the78mole/km271-wifi/DOC/KM271 Oil Burner has error.PNG

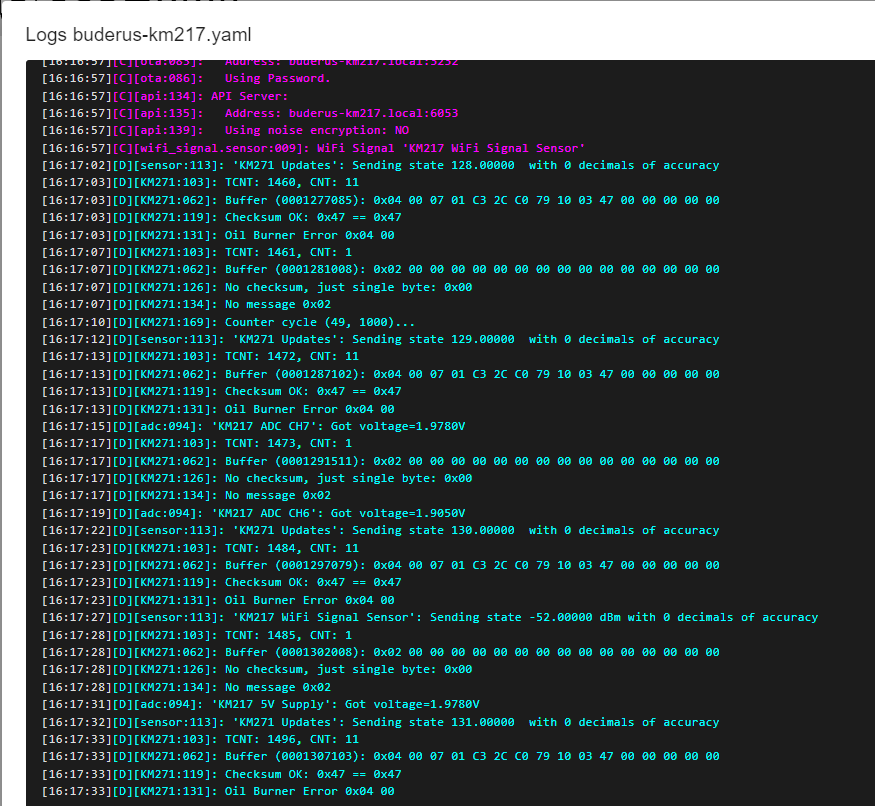
DOC/KM271 Oil Burner has error.PNG
