the78mole/km271-wifi/EXTENSIONS/ETH_W5500/Export/ETH_W5500.png

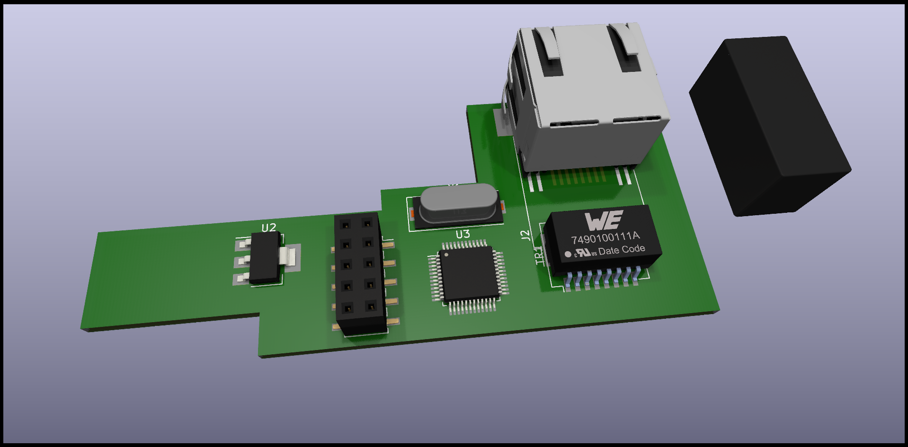
EXTENSIONS/ETH_W5500/Export/ETH_W5500.png
