the78mole/km271-wifi/EXTENSIONS/ETH_W5500/IMG/ETH_Extension_Rendering.PNG

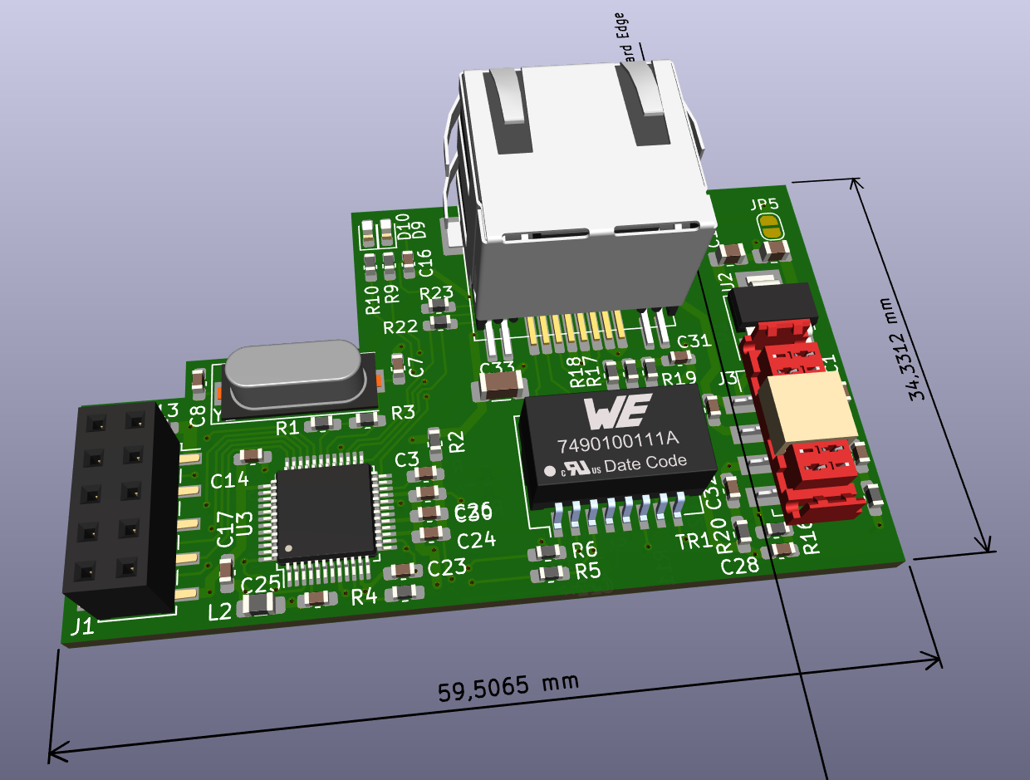
EXTENSIONS/ETH_W5500/IMG/ETH_Extension_Rendering.PNG
