the78mole/km271-wifi/IMG/FM244/FM244 Front.jpg

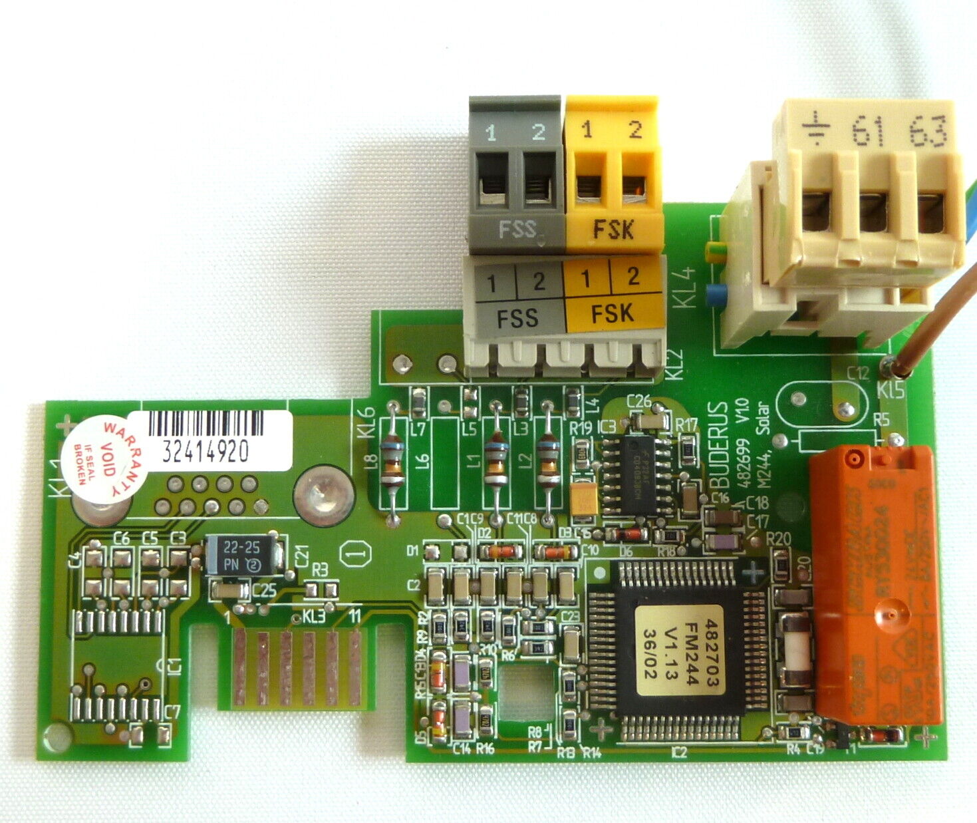
IMG/FM244/FM244 Front.jpg
