the78mole/km271-wifi/IMG/IMG_20220502_030331.jpg

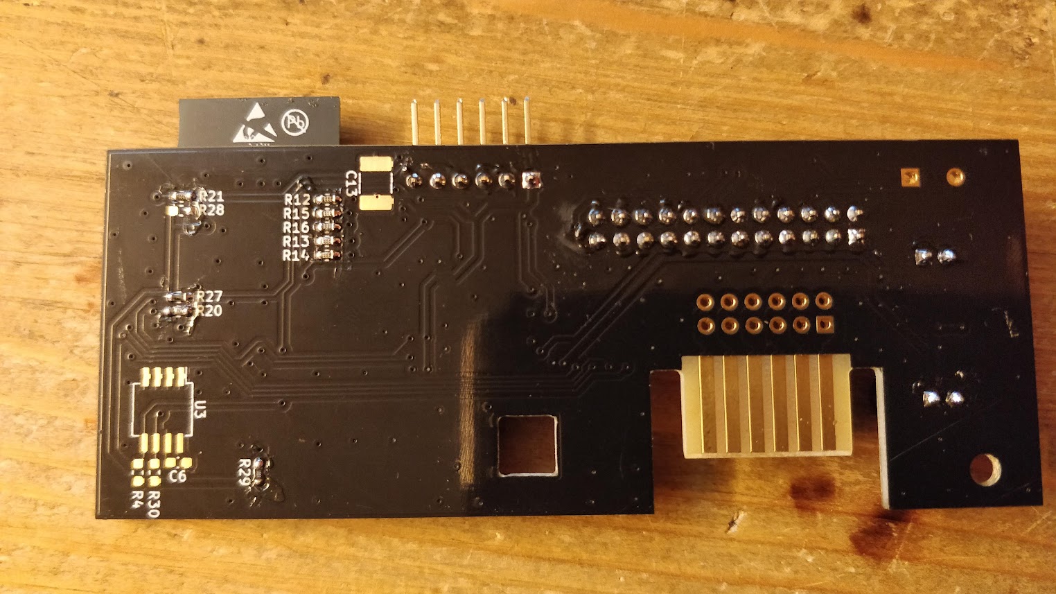
IMG/IMG_20220502_030331.jpg
