the78mole/km271-wifi/IMG/KM271-WiFi-0.0.6.jpg

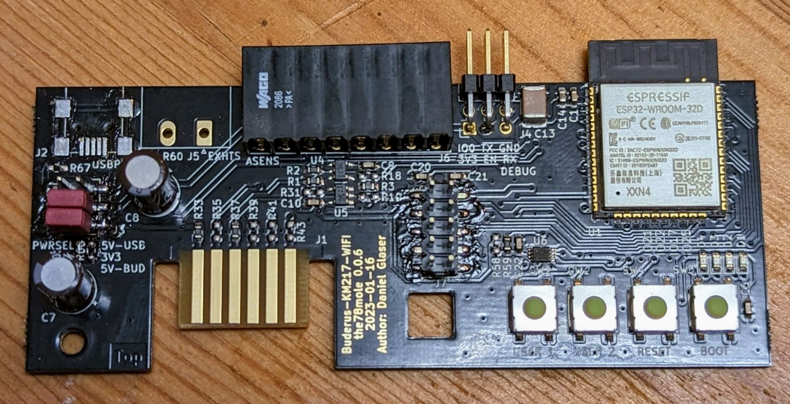
IMG/KM271-WiFi-0.0.6.jpg
