the78mole/km271-wifi/IMG/KM271-WiFi-0.0.7 Back.jpg

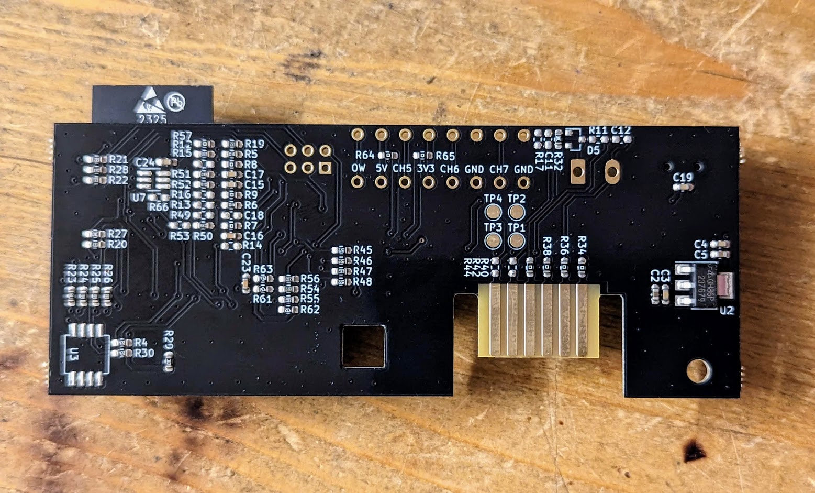
IMG/KM271-WiFi-0.0.7 Back.jpg
