the78mole/km271-wifi/IMG/KM271-WiFi-0.0.7_3D.png

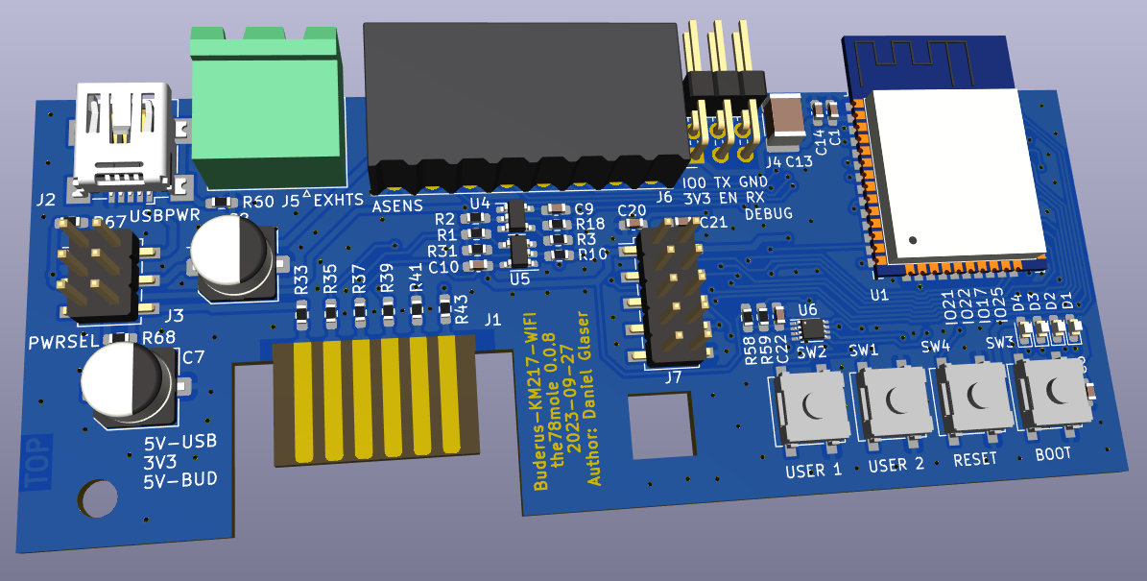
IMG/KM271-WiFi-0.0.7_3D.png
