the78mole/km271-wifi/IMG/KM271-WiFi-0.1.0-back.jpg

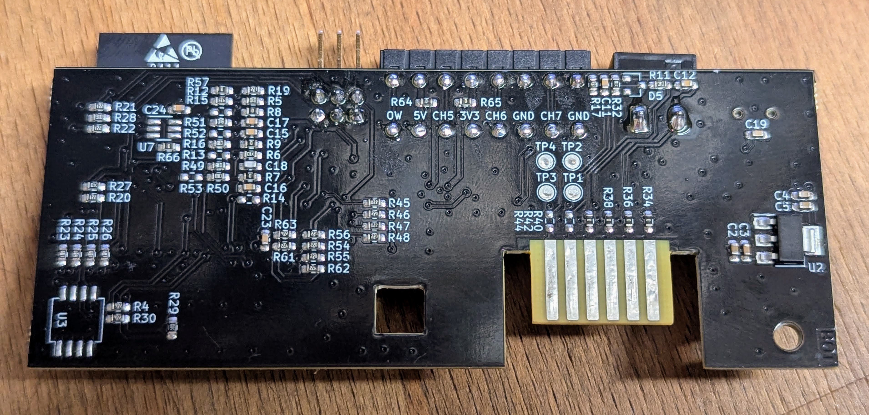
IMG/KM271-WiFi-0.1.0-back.jpg
