the78mole/km271-wifi/IMG/KM271-WiFi_0.0.5_top.jpg

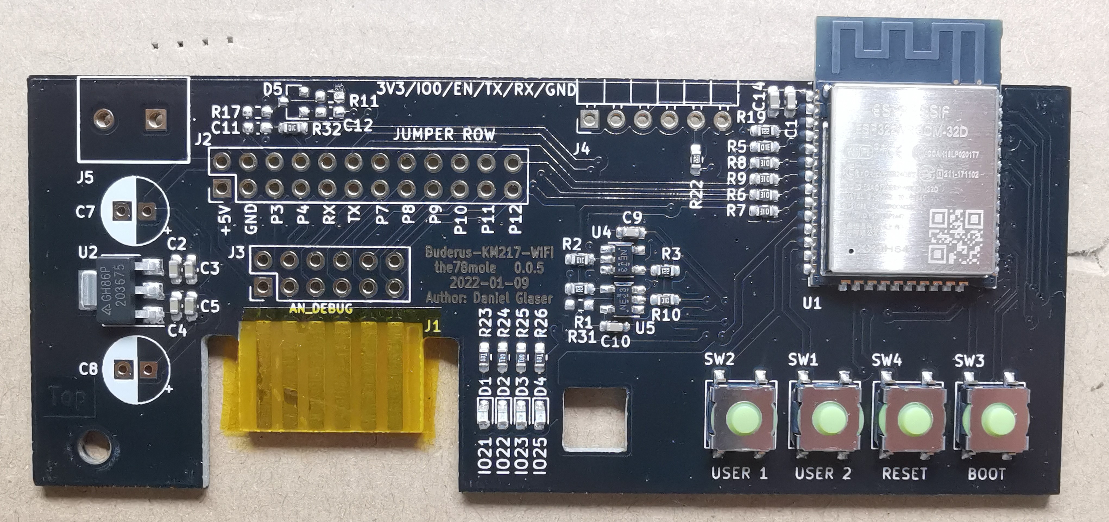
IMG/KM271-WiFi_0.0.5_top.jpg
