the78mole/km271-wifi/IMG/M292/M292_bottom_crop.jpg

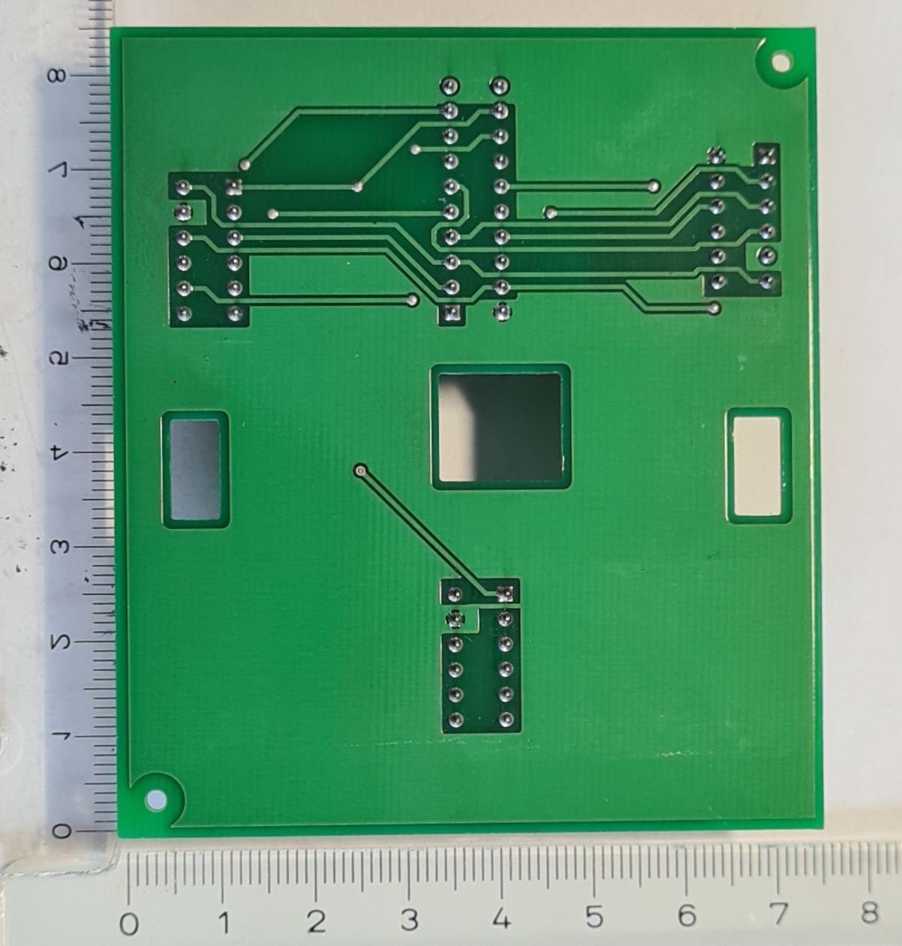
IMG/M292/M292_bottom_crop.jpg
