the78mole/km271-wifi/IMG/M292/M292_top_2_crop.jpg

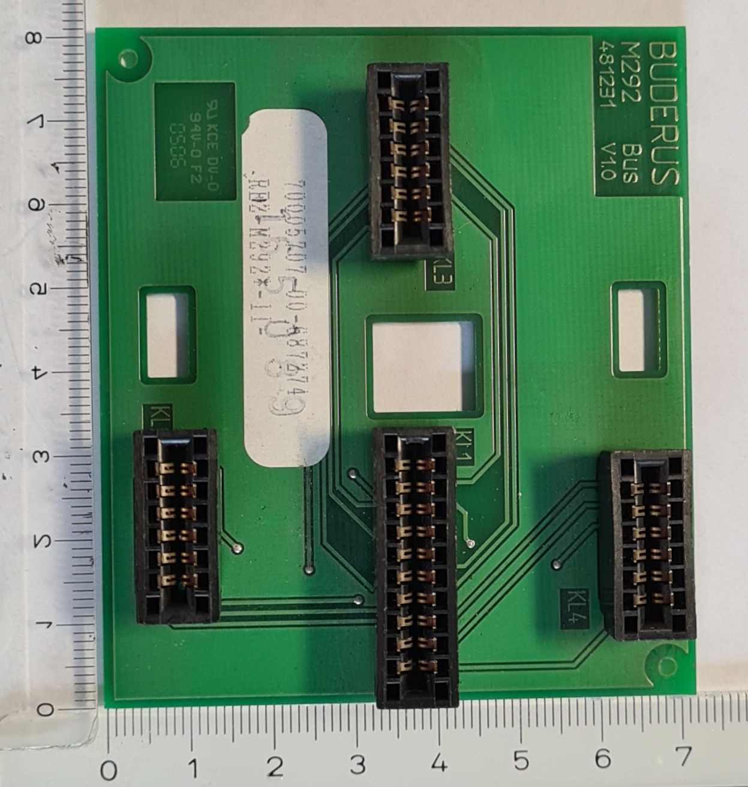
IMG/M292/M292_top_2_crop.jpg
