the78mole/km271-wifi/IMG/PCB_0.0.6.jpg

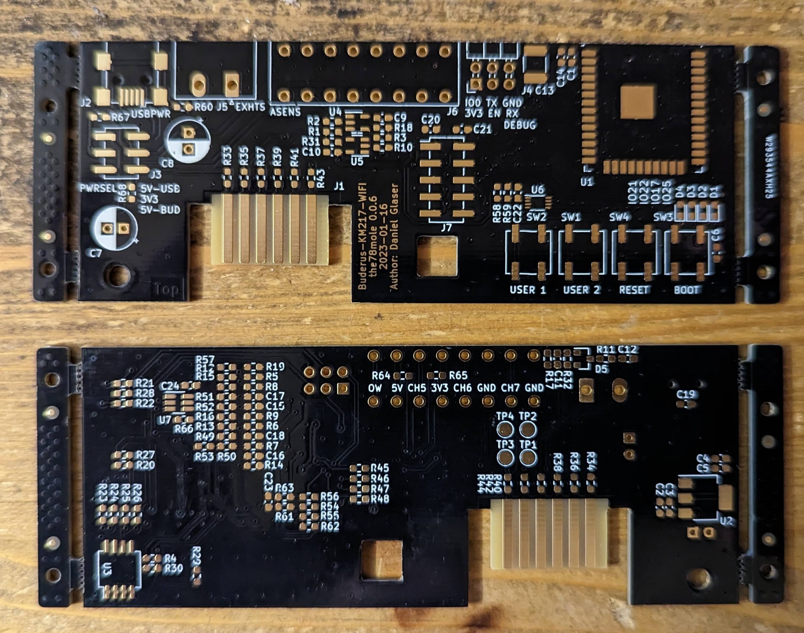
IMG/PCB_0.0.6.jpg
