the78mole/km271-wifi/EXTENSIONS/ETH_W5500/DOC/w5500_sch_v110_use_trans_.pdf

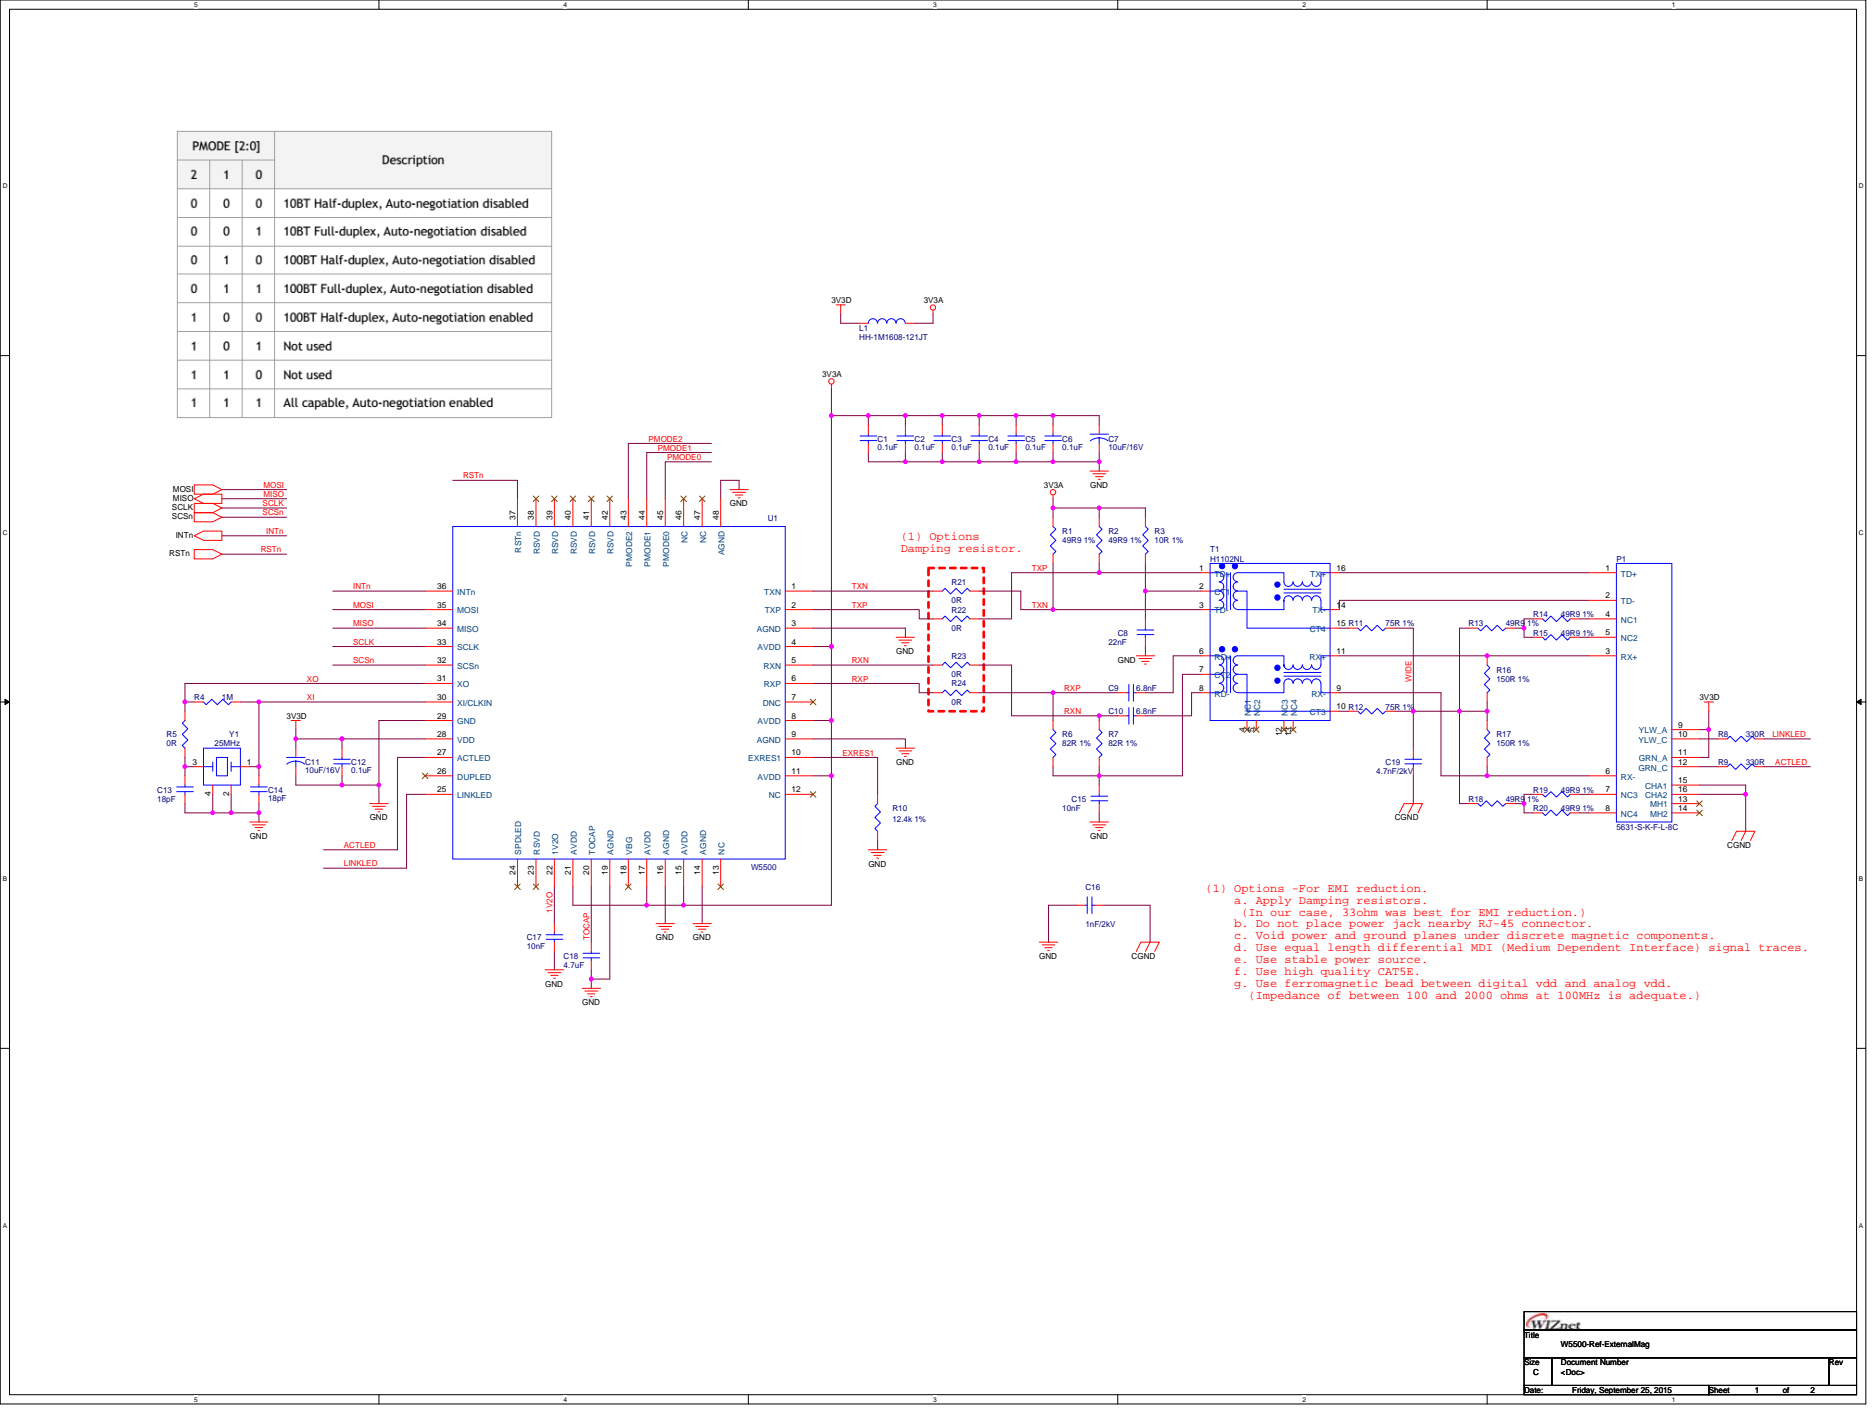
[picture p62: page 1]

(1) Options -For EMI reduction.
a. Apply Damping resistors.
(In our case, 33ohm was best for EMI reduction.)
b. Do not place power jack nearby RJ-45 connector.
c. Void power and ground planes under discrete magnetic components.
d. Use equal length differential MDI (Medium Dependent Interface) signal traces.
e. Use stable power source.
f. Use high quality CAT5E.
g. Use ferromagnetic bead between digital vdd and analog vdd.
(Impedance of between 100 and 2000 ohms at 100MHz is adequate.)
