the78mole/km271-wifi/EXTENSIONS/ETH_W5500/Export/ETH_W5500.pdf

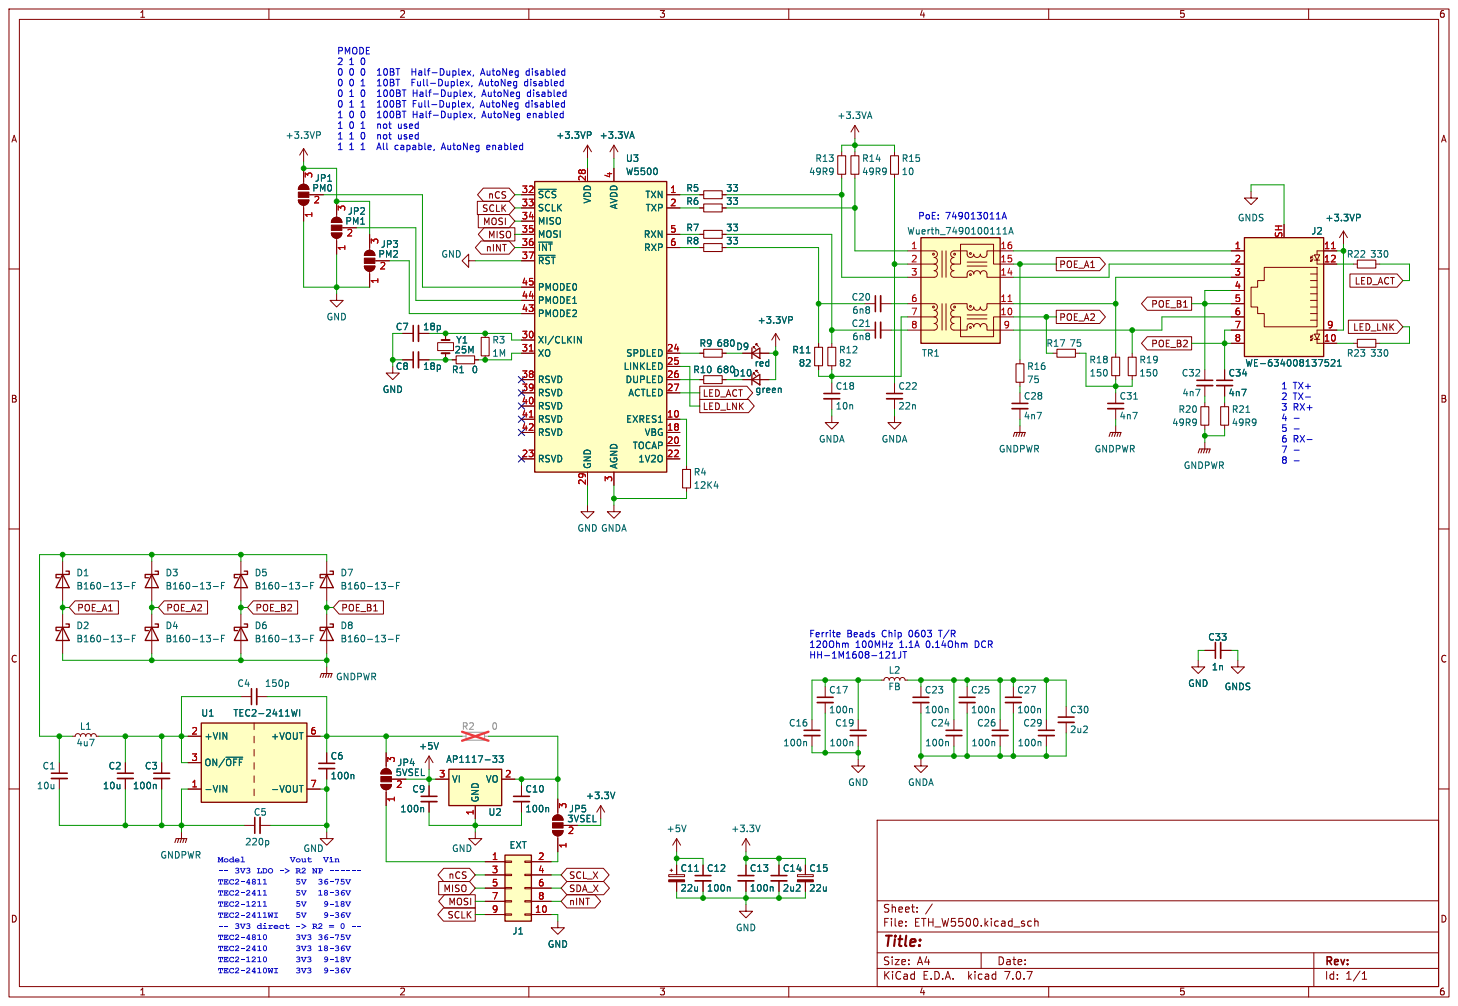
[picture p63: page 1]

4 RSVD 40 RSVD 41 RSVD 42 PMODE2 43 PMODE1 44 PMODE0 45 RXN 5 RXP 6 U3 W5500 R22 330 C34

4 RSVD 40 RSVD 41 RSVD 42 PMODE2 43 PMODE1 44 PMODE0 45 RXN 5 RXP 6 D10 GND green

3 XI/CLKIN 30 XO 31 ~{SCS} 32 SCLK 33 MISO 34 MOSI 35 ~{INT} 36 ~{RST} 37 RSVD 38 RSVD 39 AVDD

4 - 5 - 6 RX- 7 - 8 - Ferrite Beads Chip 0603 T/R
