the78mole/km271-wifi/KM217-WiFi/Export/KM217-WiFi - PCB 0.0.7.pdf

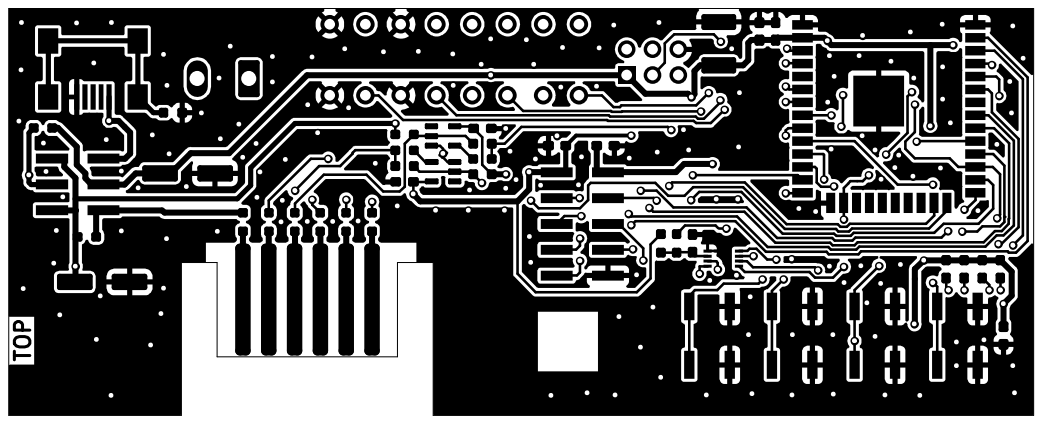
[picture p66: page 1]

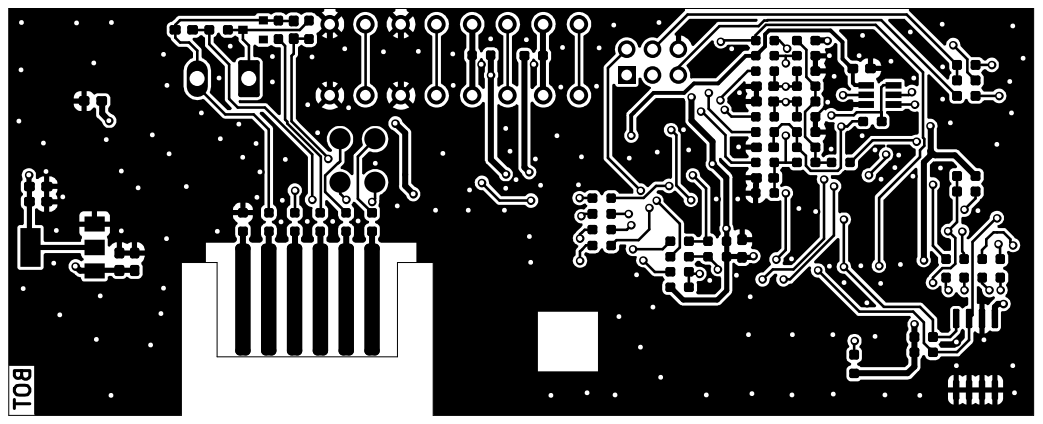
[picture p67: page 2]

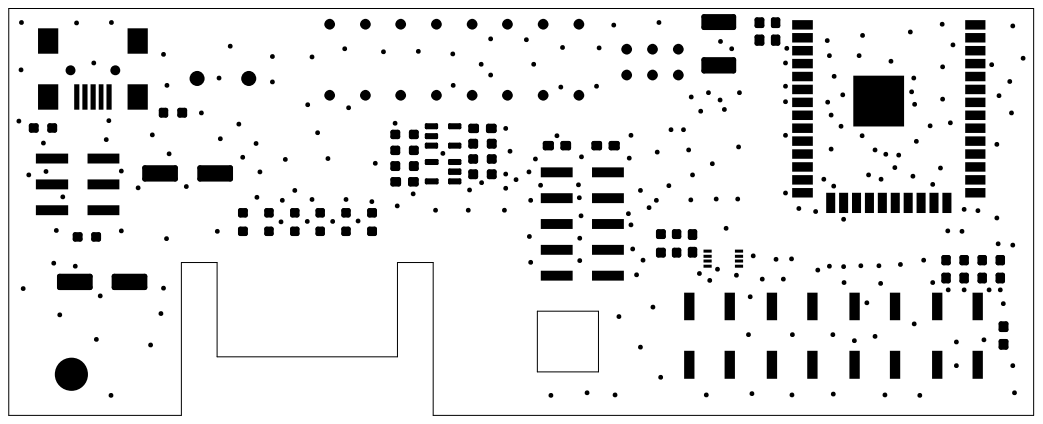
[picture p68: page 3]

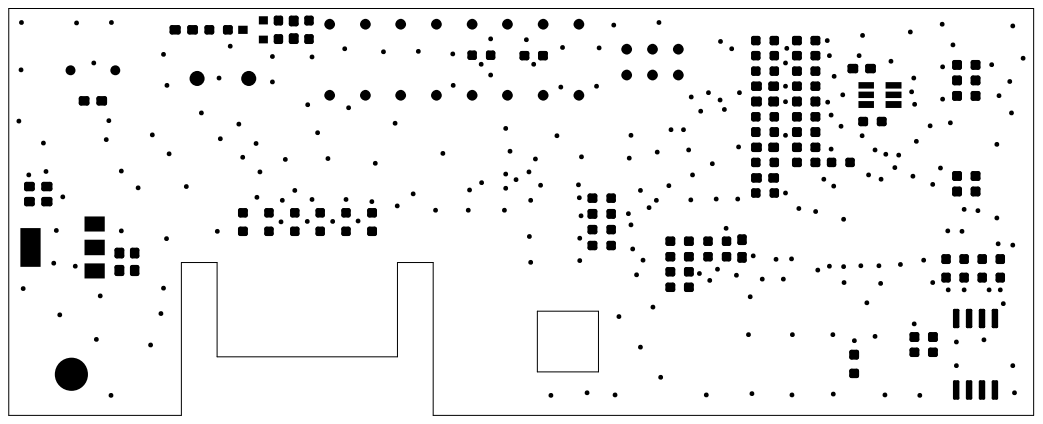
[picture p69: page 4]

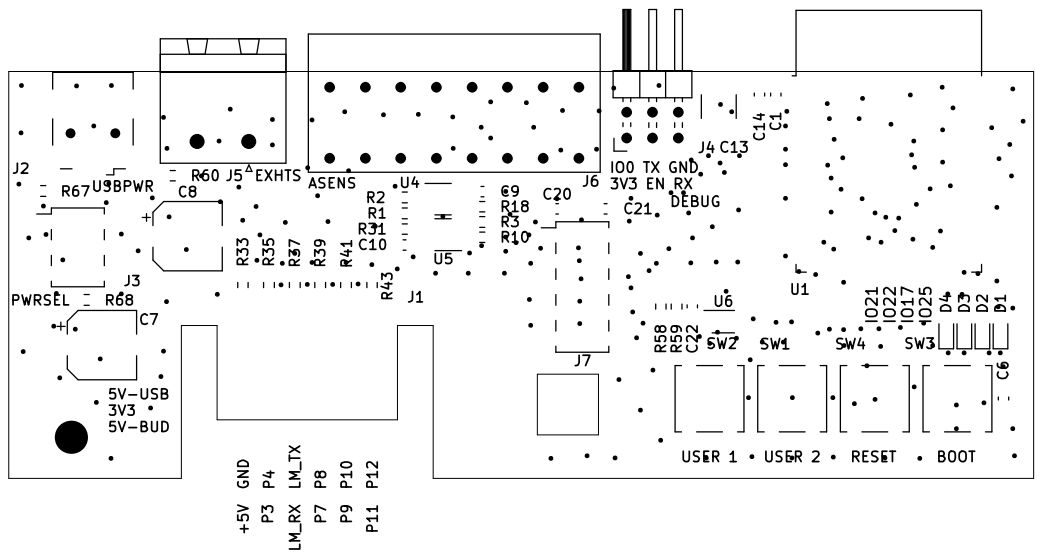
[picture p70: page 5]

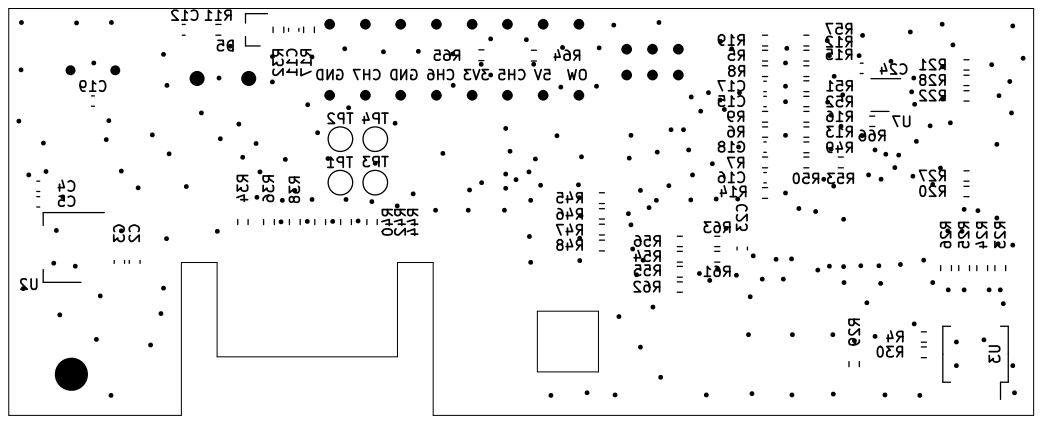
[picture p71: page 6]

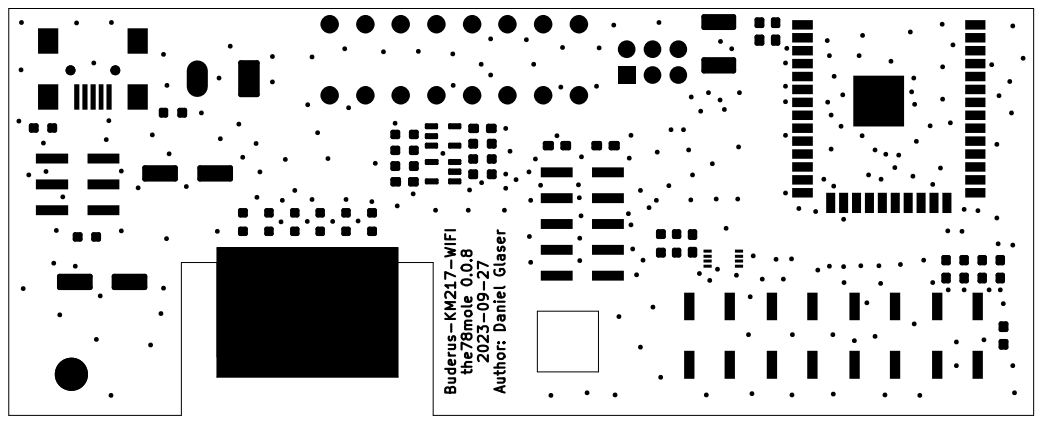
[picture p72: page 7]

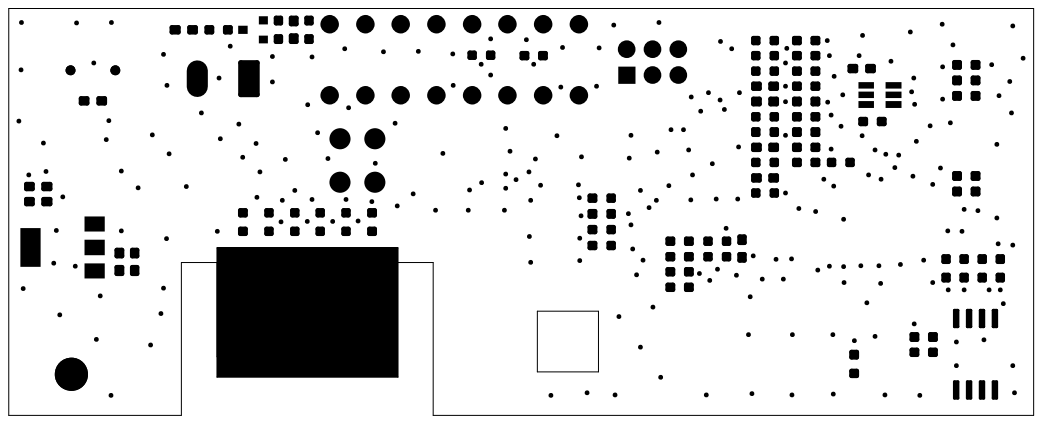
[picture p73: page 8]

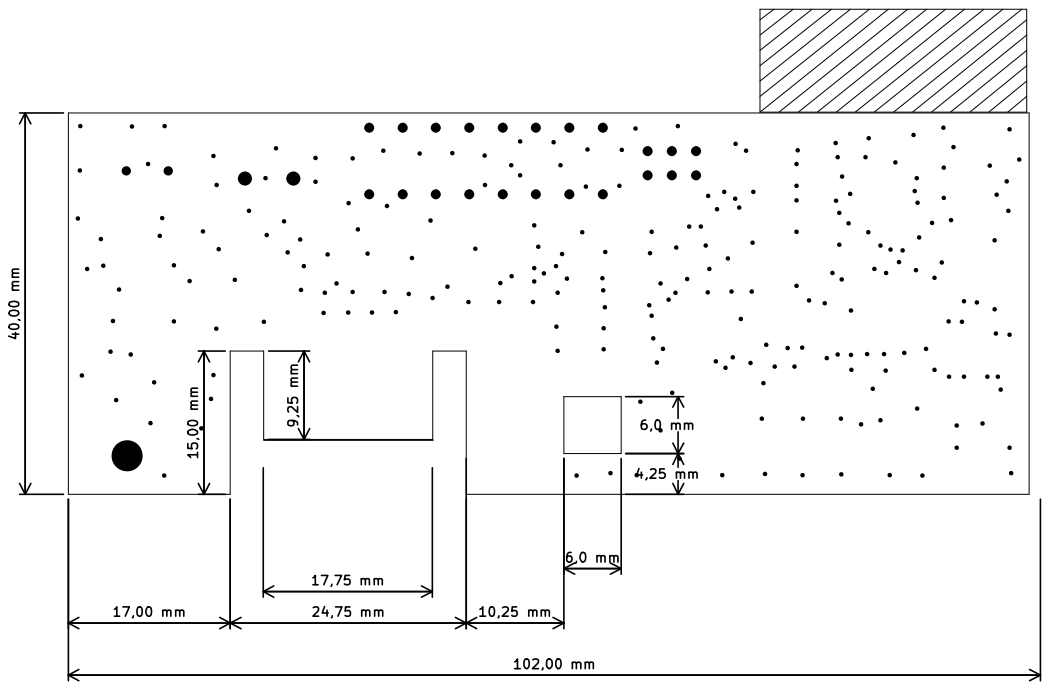
[picture p74: page 9]

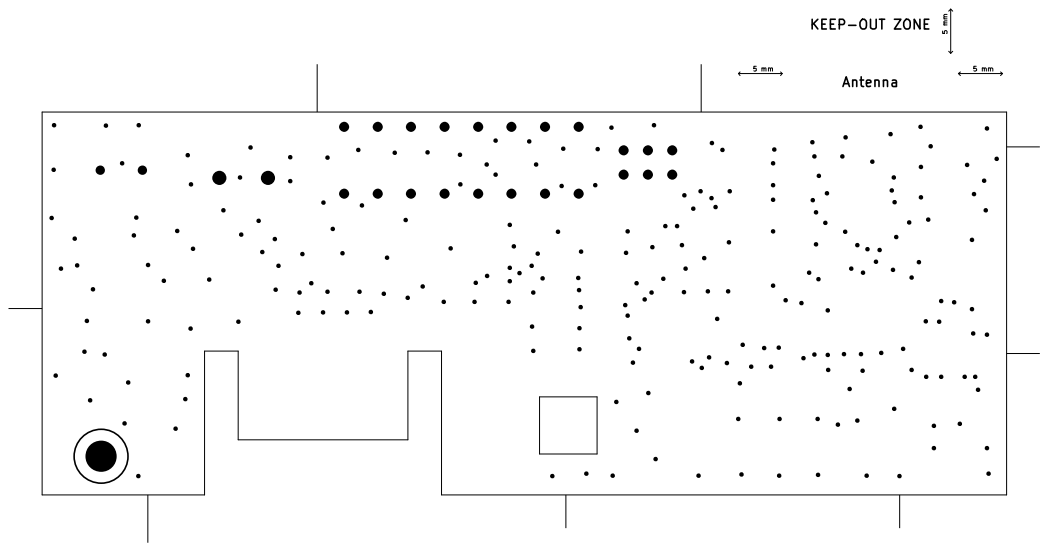
[picture p75: page 10]

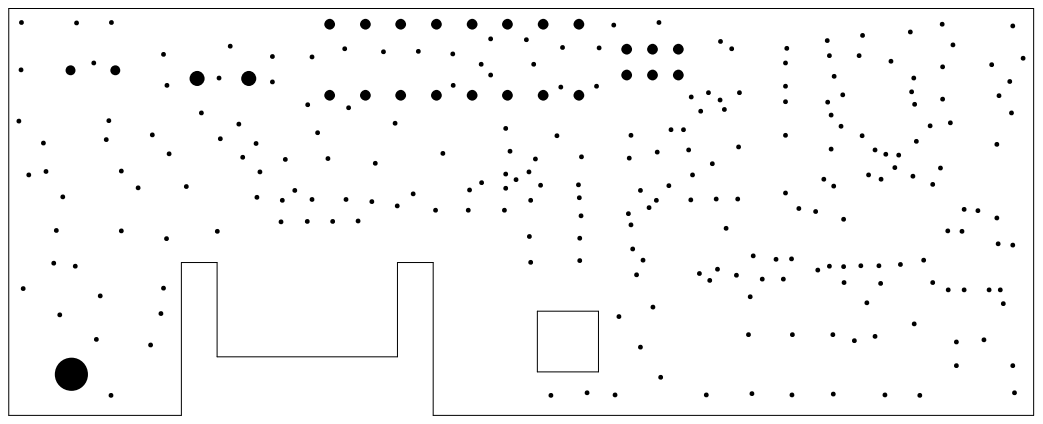
[picture p76: page 11]

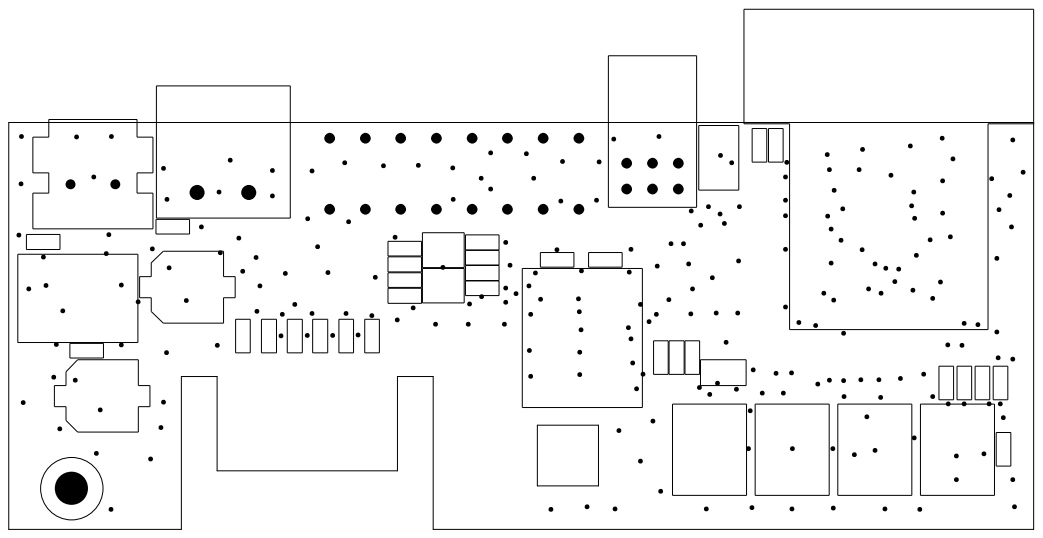
[picture p77: page 13]

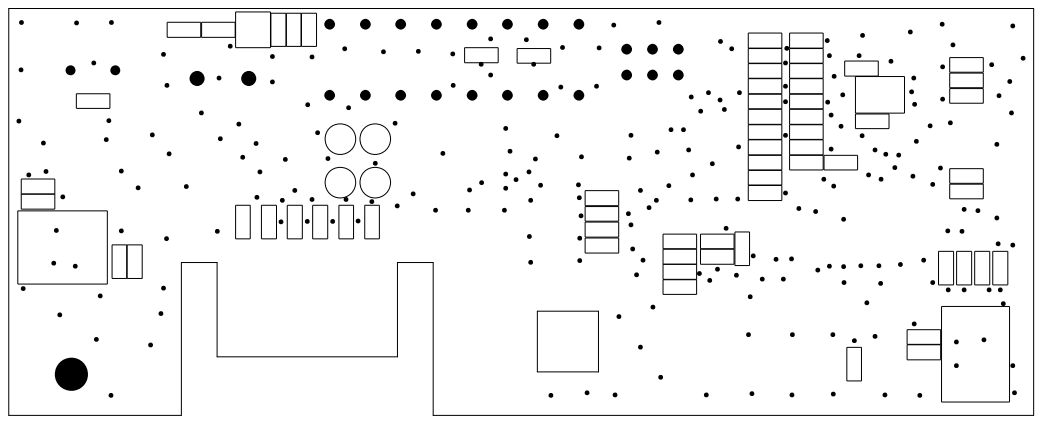
[picture p78: page 14]

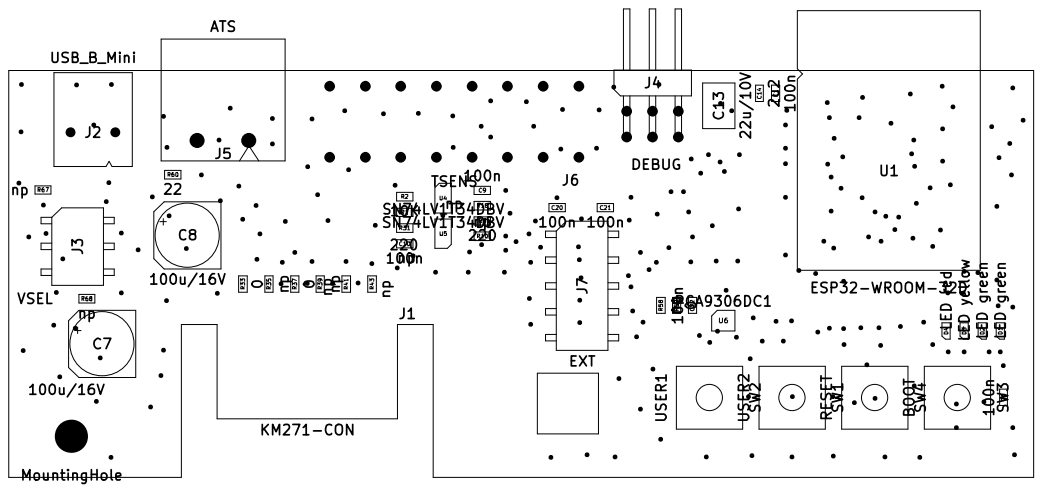
[picture p79: page 15]

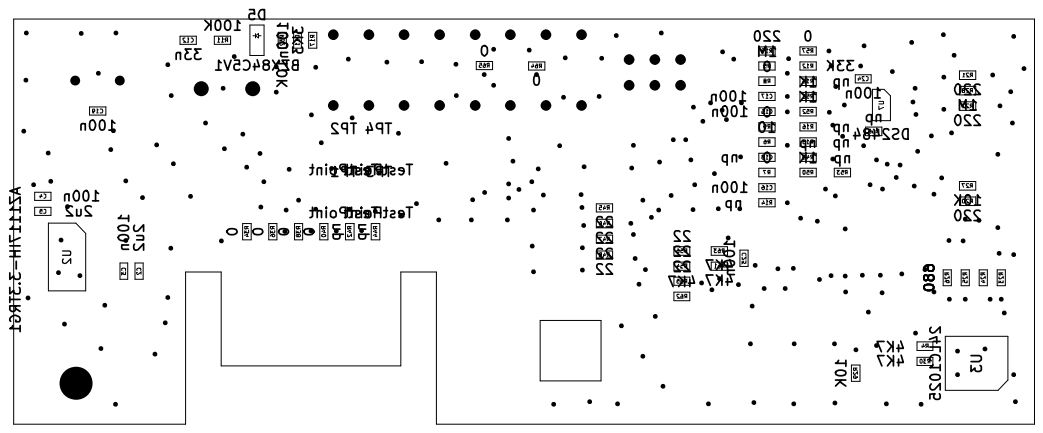
[picture p80: page 16]
