the78mole/km271-wifi/KM217-WiFi/Export/KM217-WiFi - PCB 0.0.5.pdf

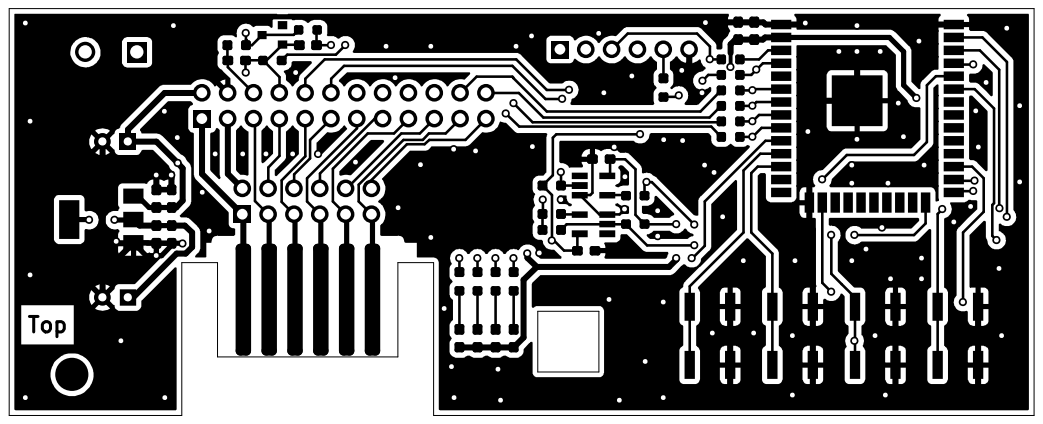
[picture p81: page 1]

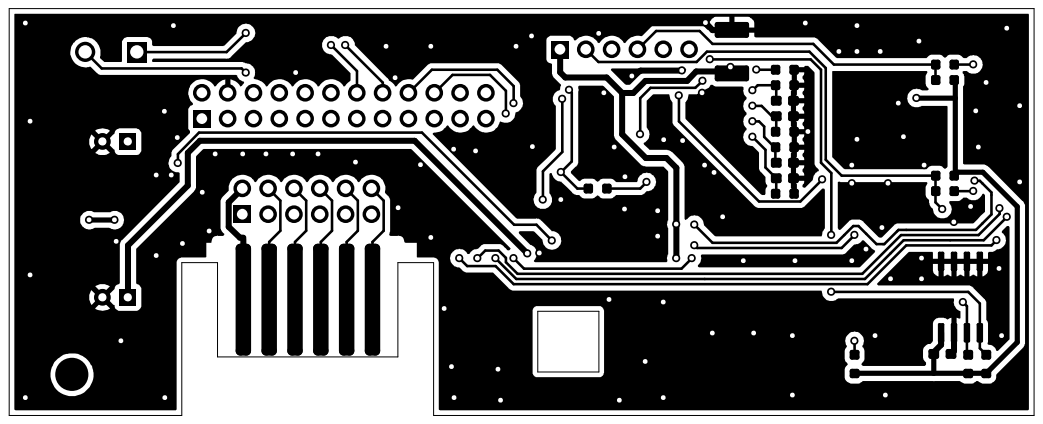
[picture p82: page 2]

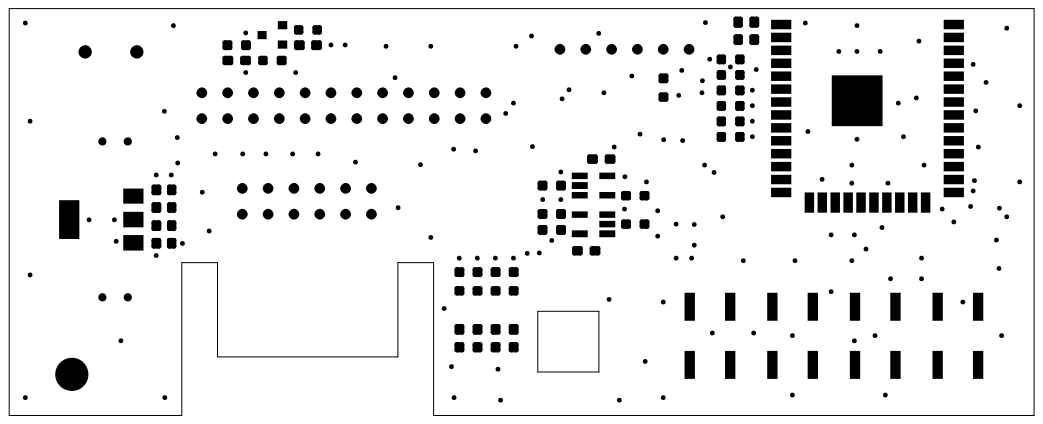
[picture p83: page 3]

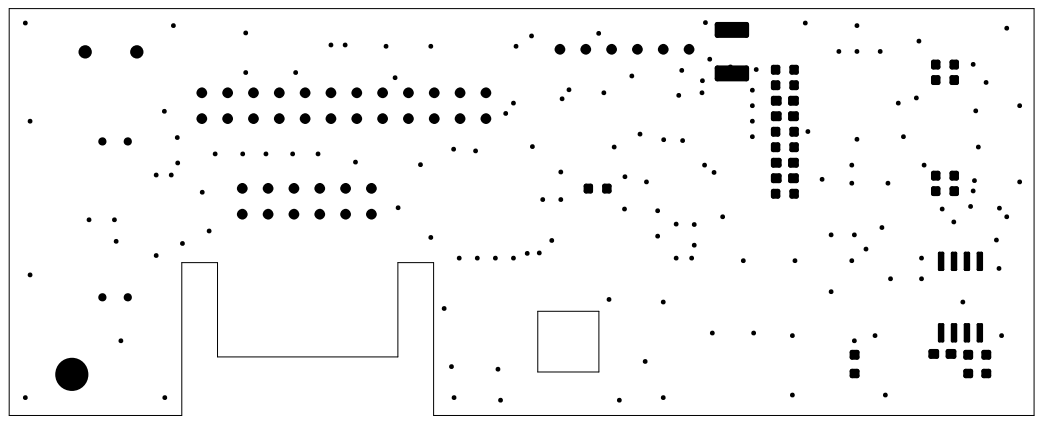
[picture p84: page 4]

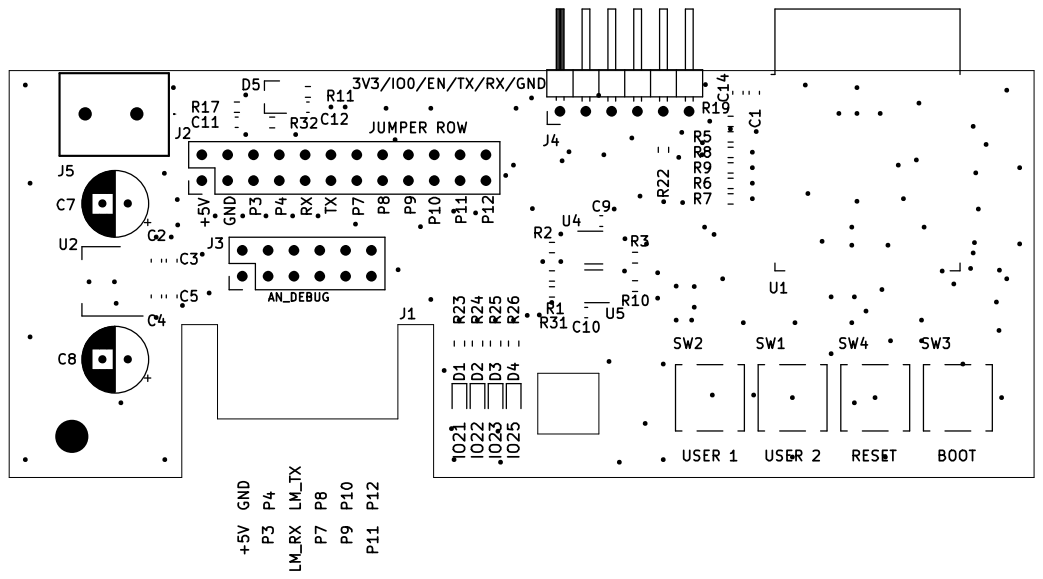
[picture p85: page 5]

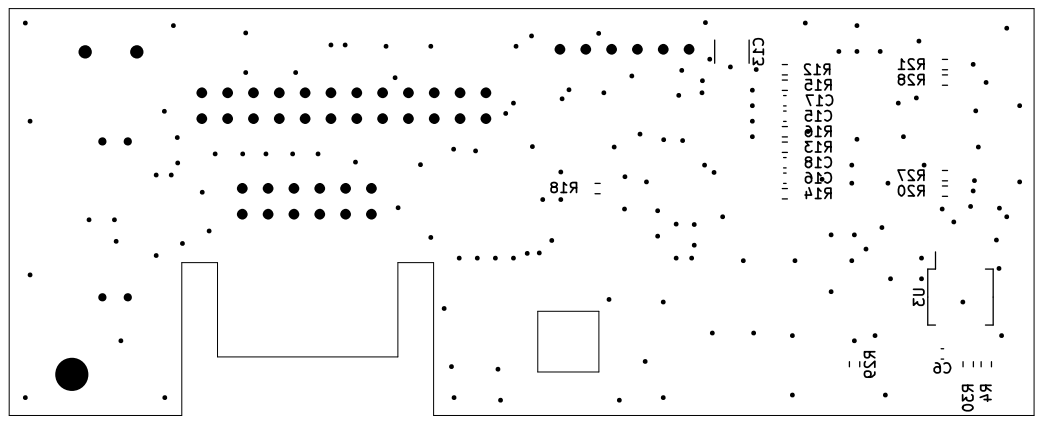
[picture p86: page 6]

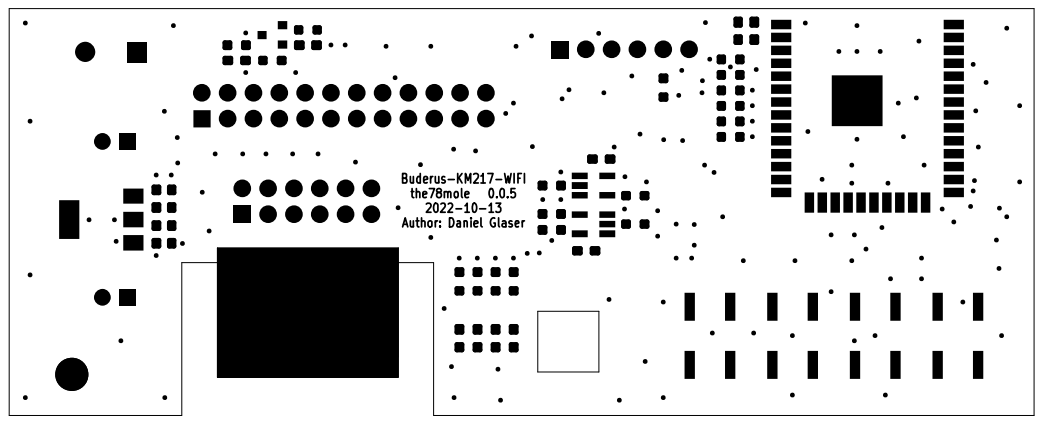
[picture p87: page 7]

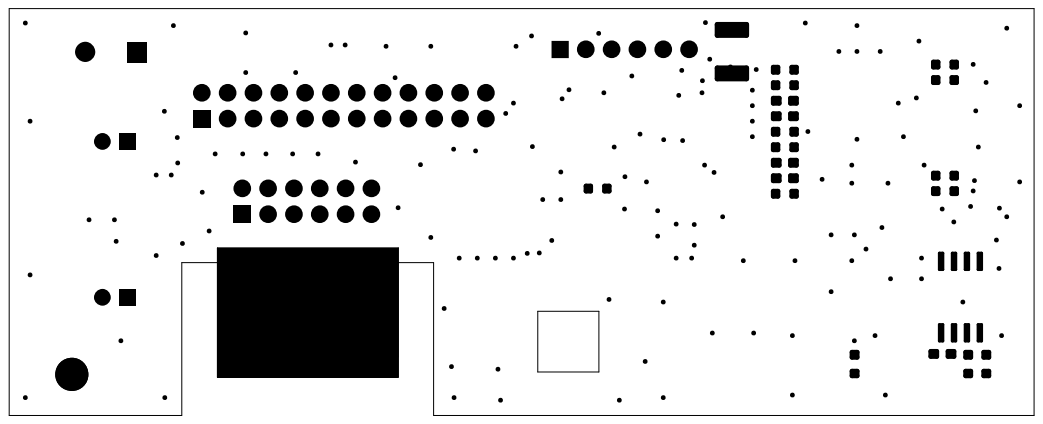
[picture p88: page 8]

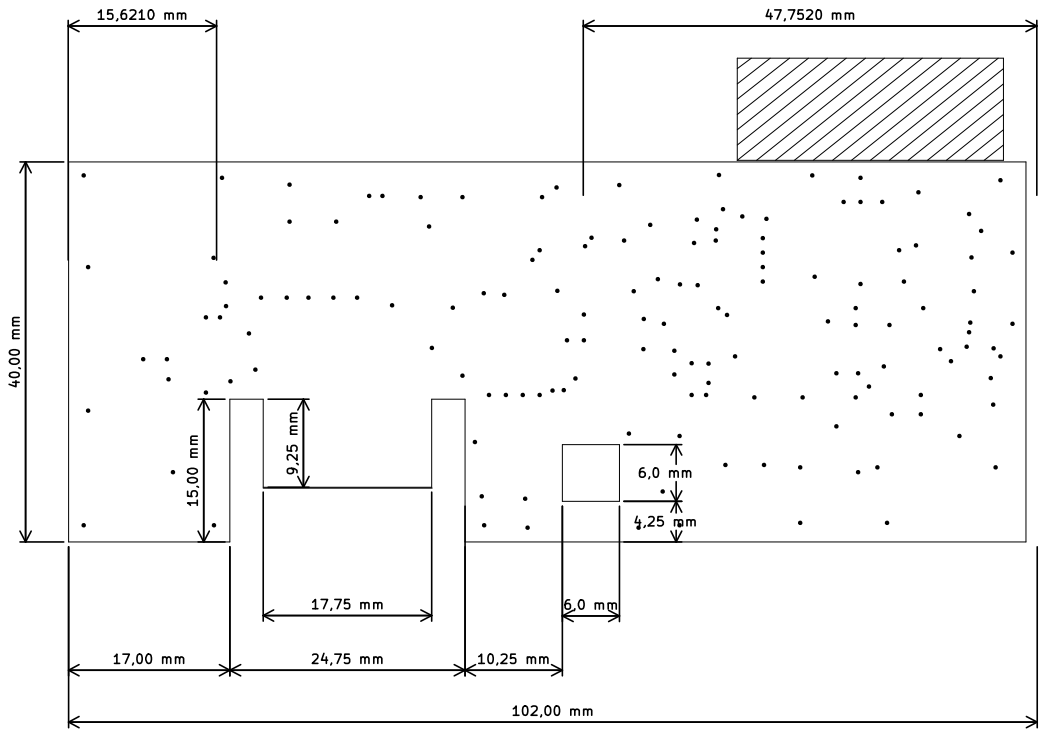
[picture p89: page 9]

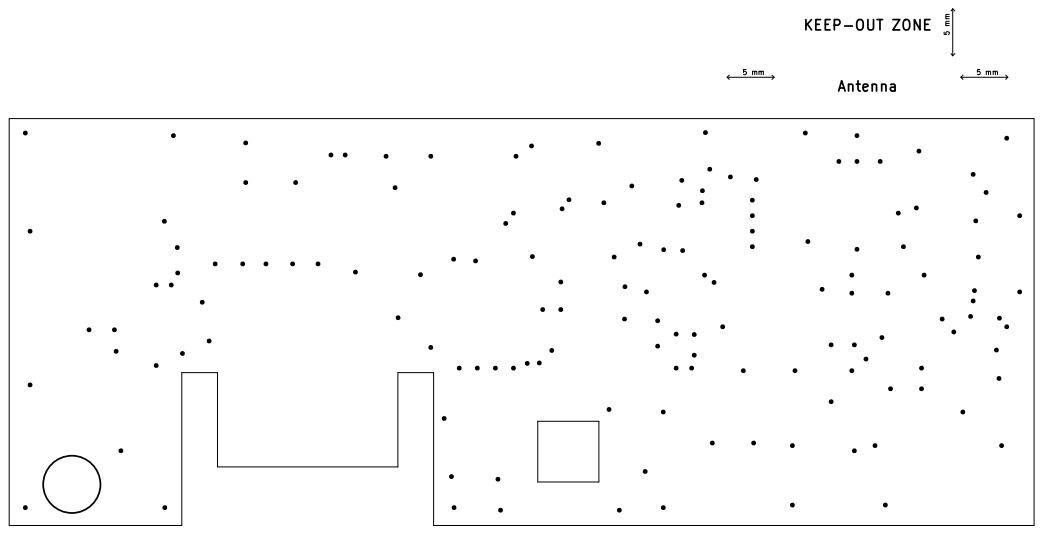
[picture p90: page 10]

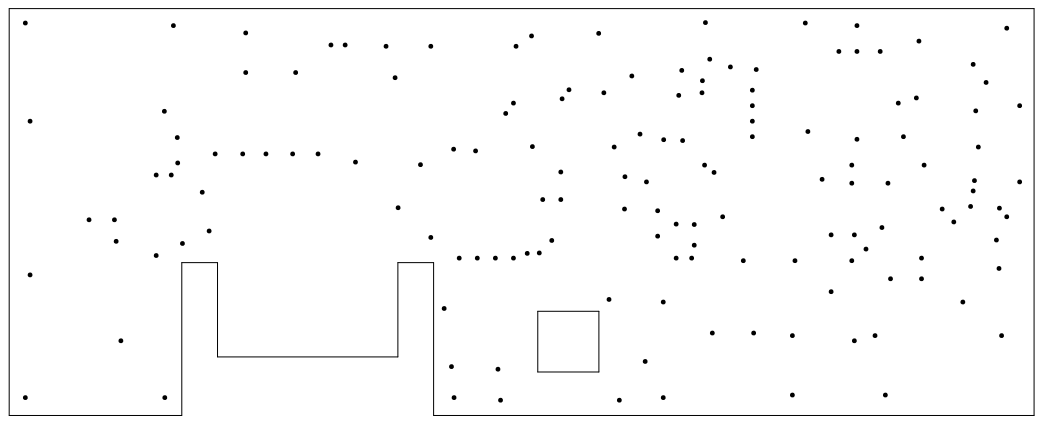
[picture p91: page 11]

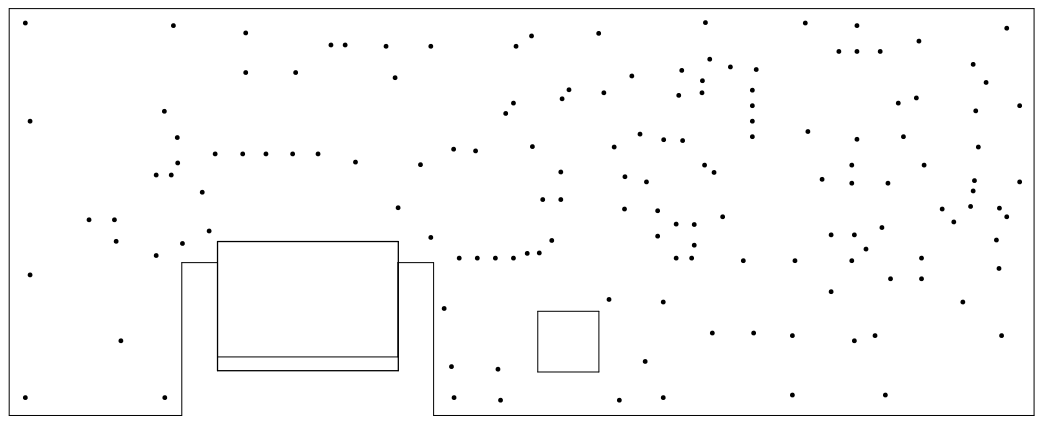
[picture p92: page 12]

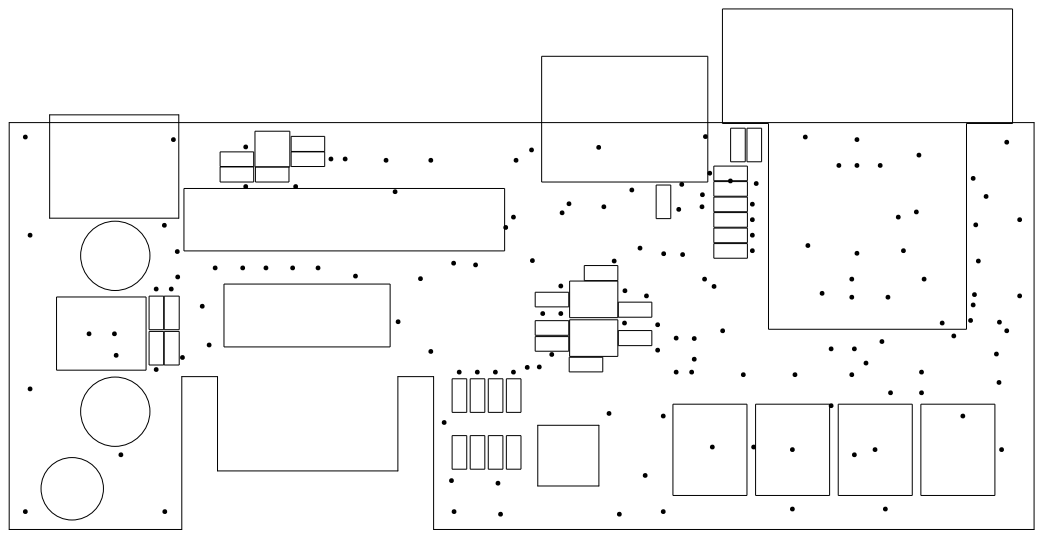
[picture p93: page 13]

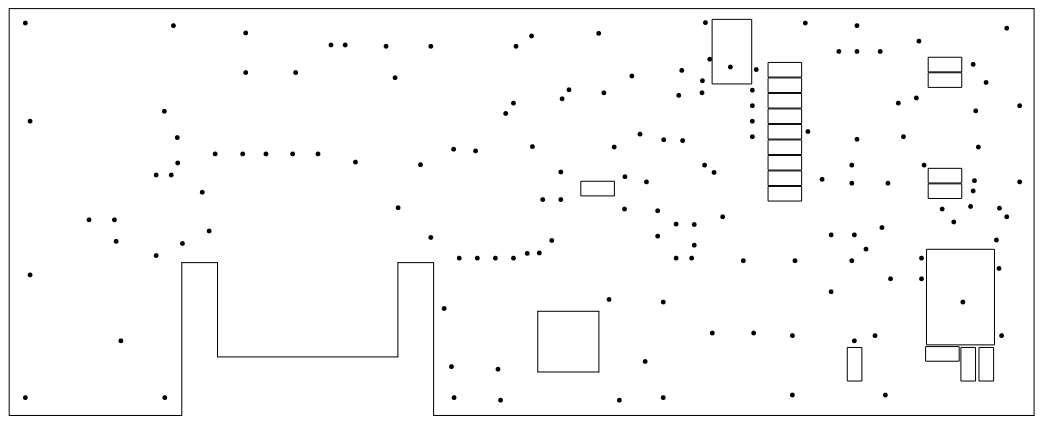
[picture p94: page 14]

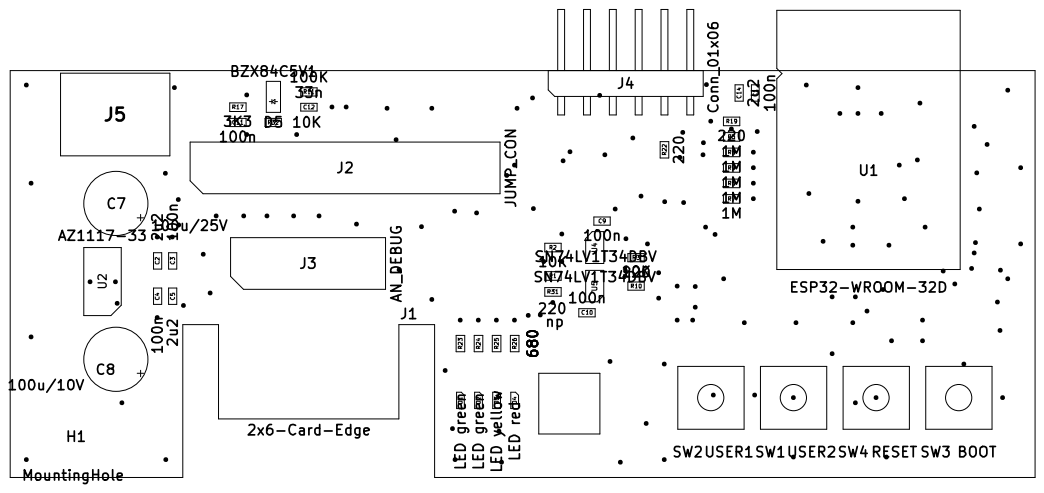
[picture p95: page 15]

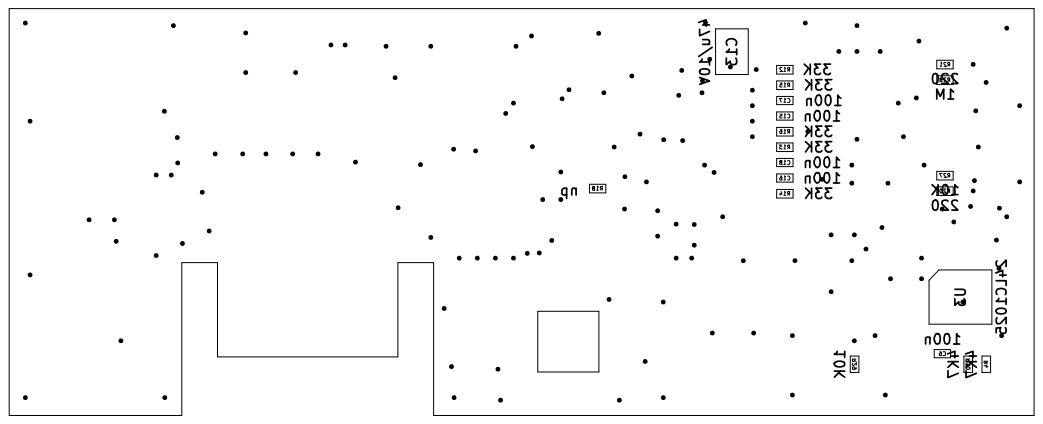
[picture p96: page 16]
