the78mole/km271-wifi/KM217-WiFi/Export/KM217-WiFi - PCB 0.0.6.pdf

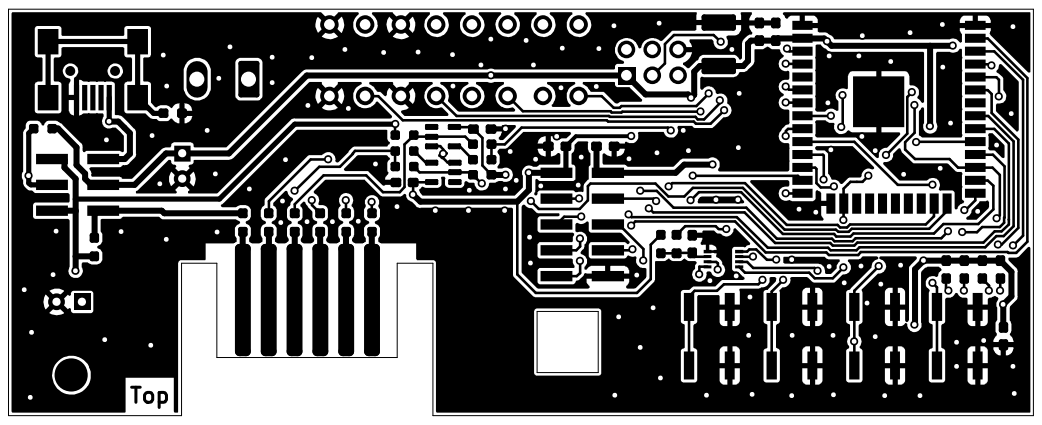
[picture p97: page 1]

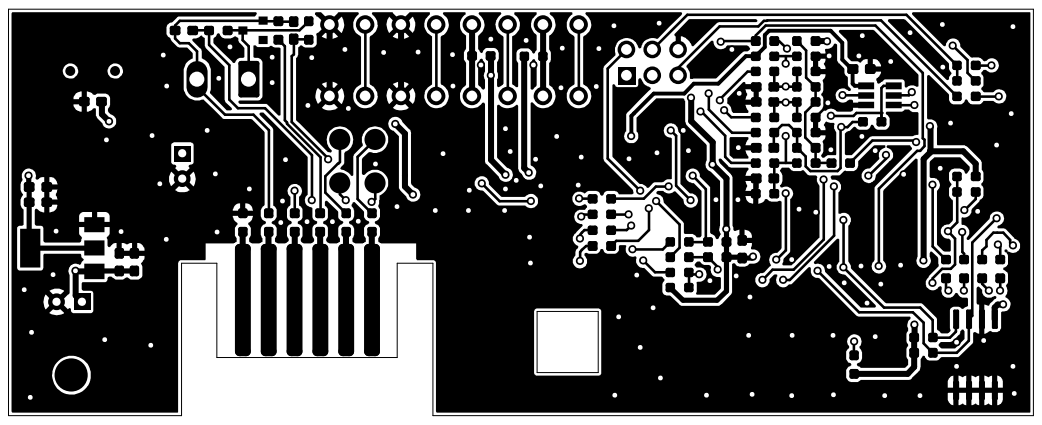
[picture p98: page 2]

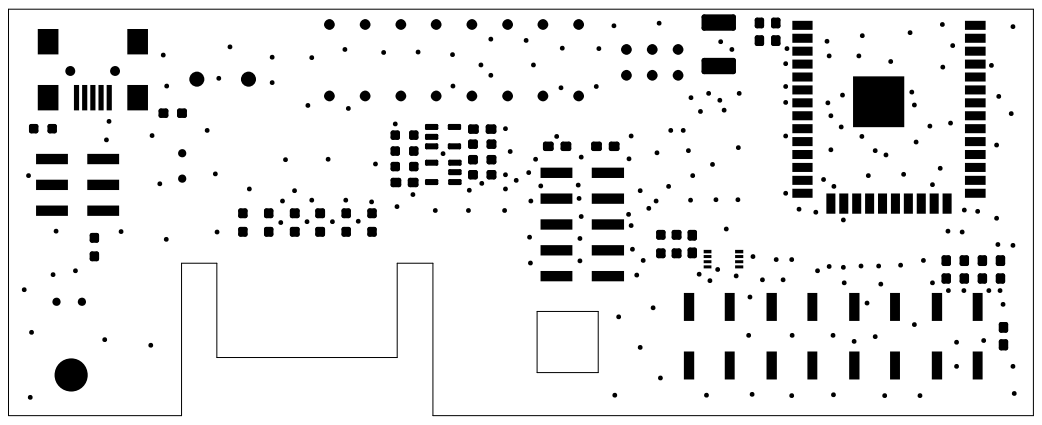
[picture p99: page 3]

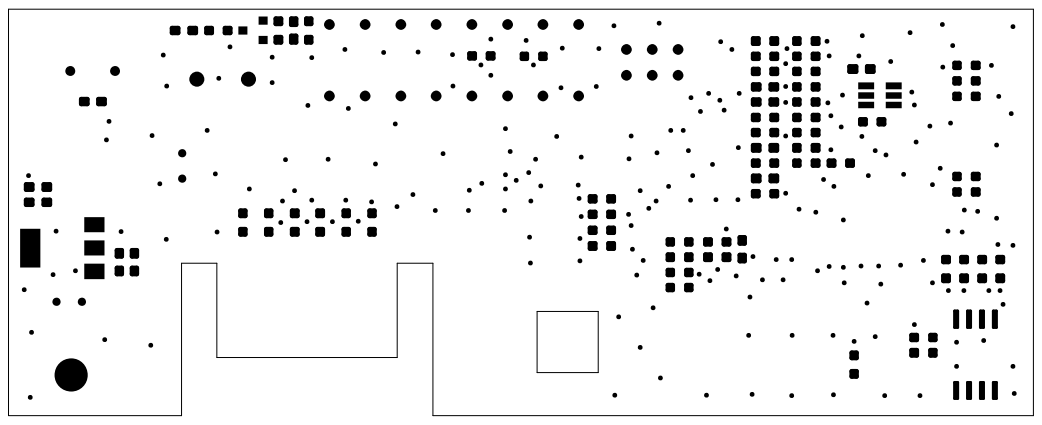
[picture p100: page 4]

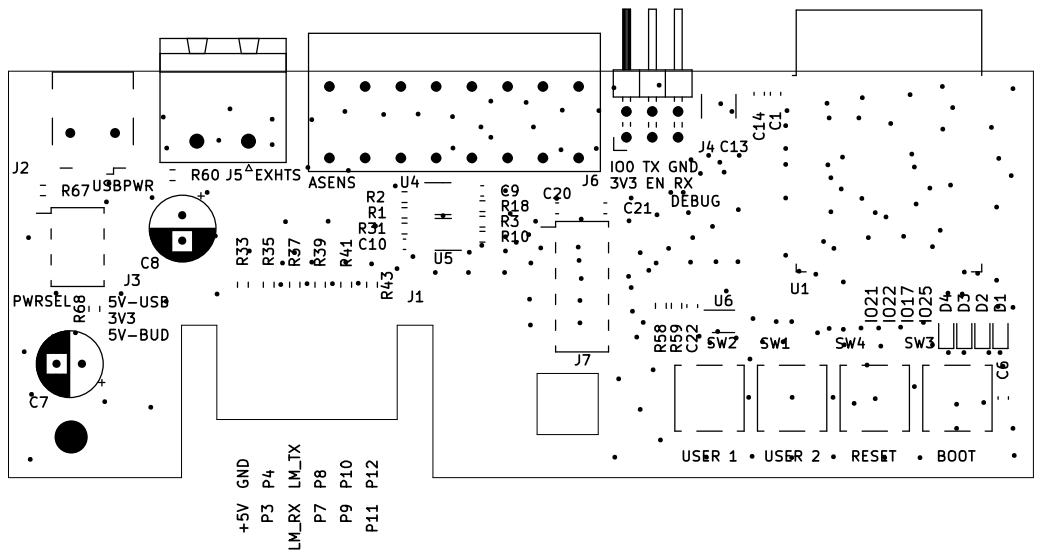
[picture p101: page 5]

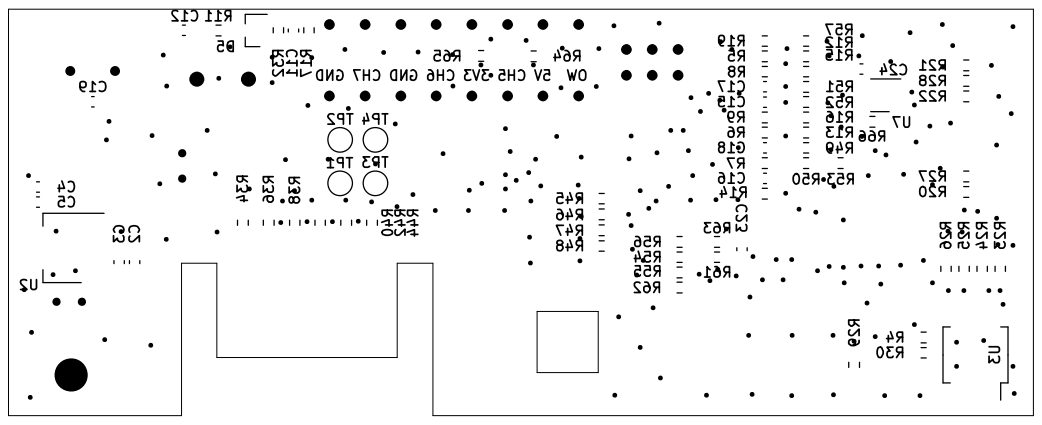
[picture p102: page 6]

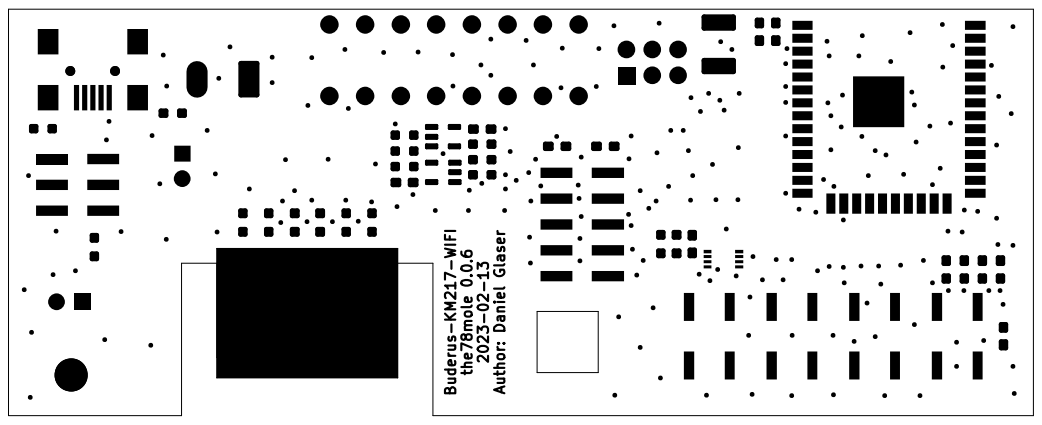
[picture p103: page 7]

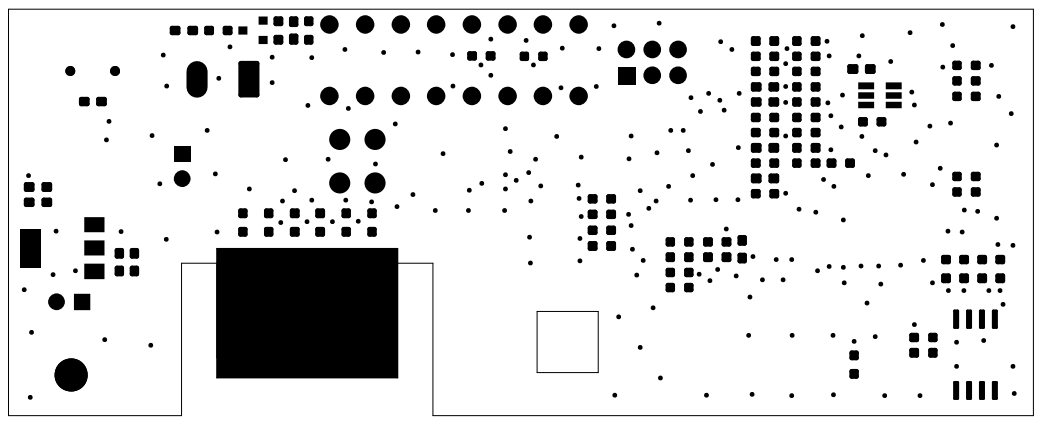
[picture p104: page 8]

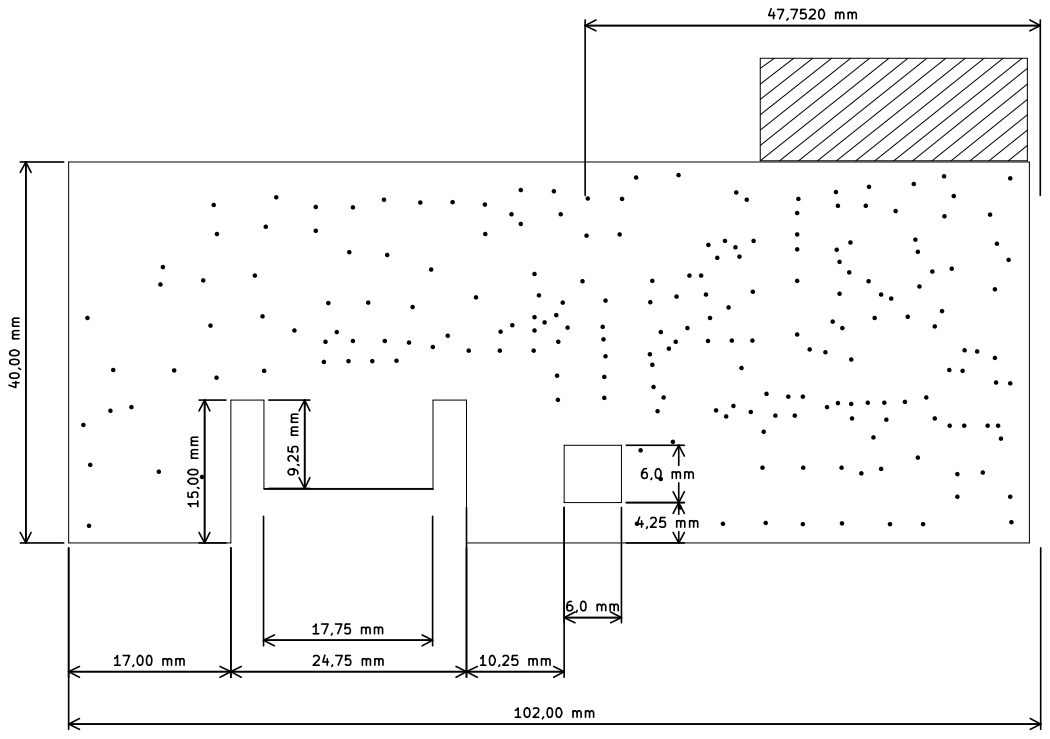
[picture p105: page 9]

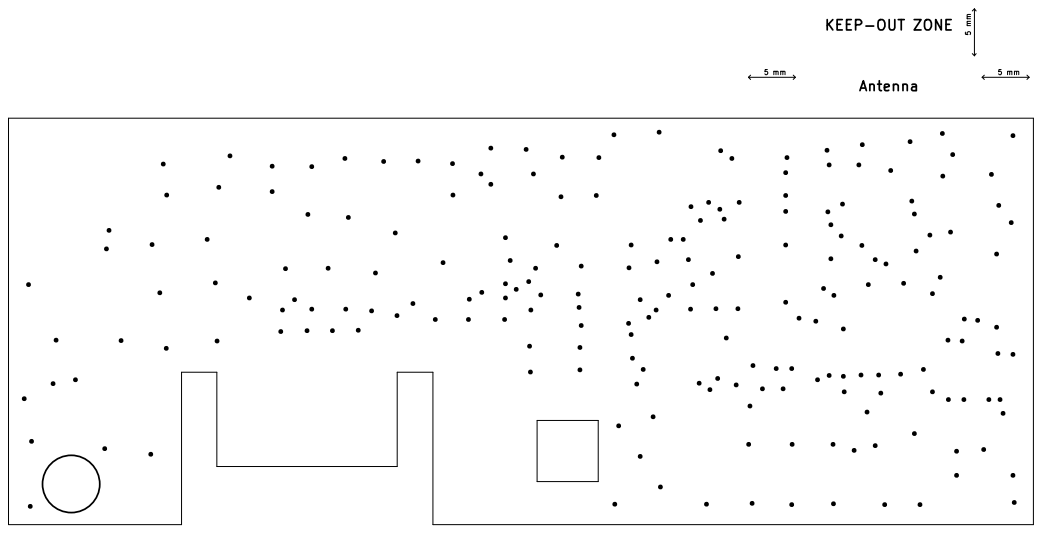
[picture p106: page 10]

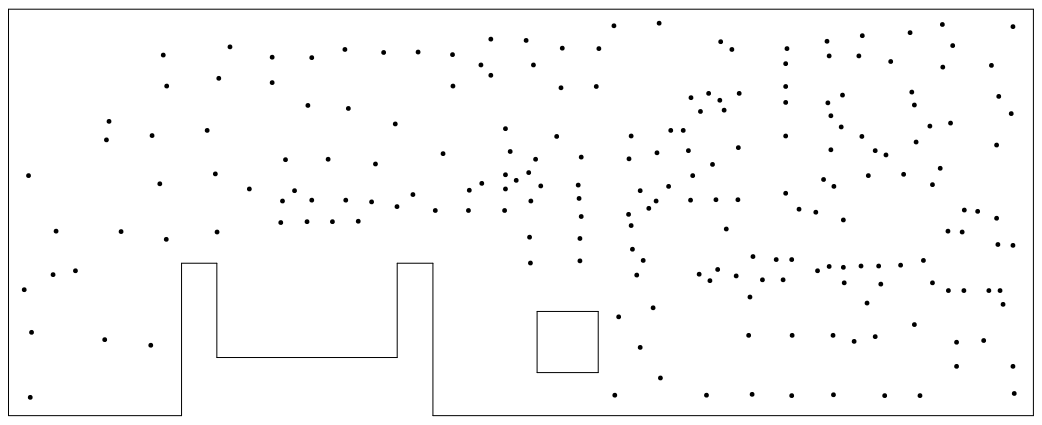
[picture p107: page 11]

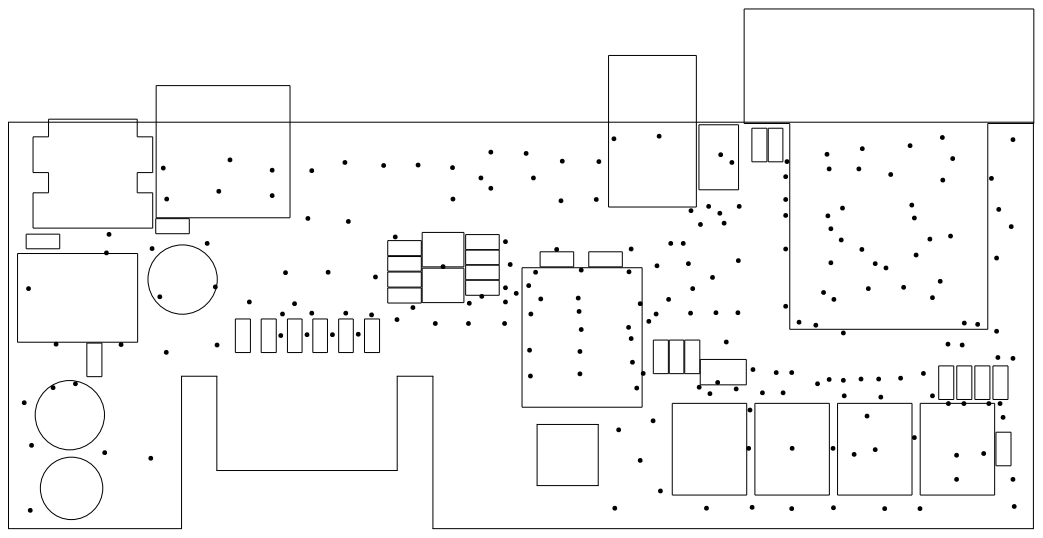
[picture p108: page 13]

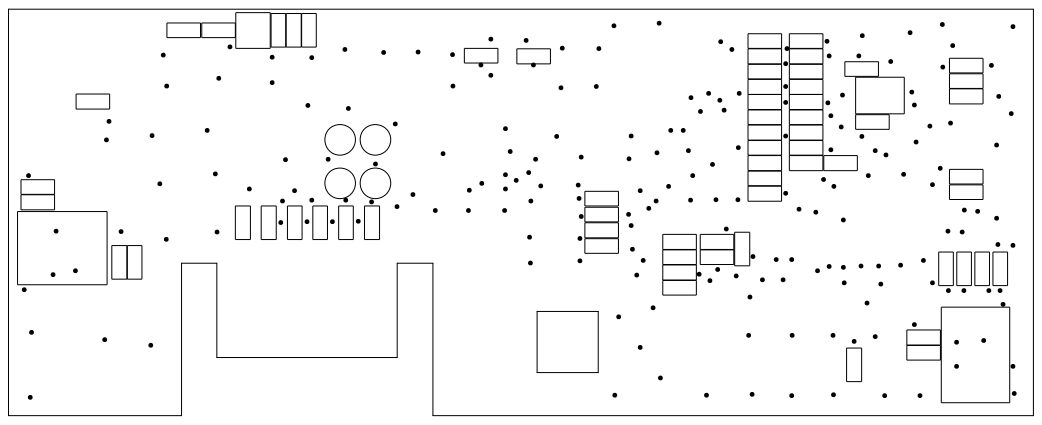
[picture p109: page 14]

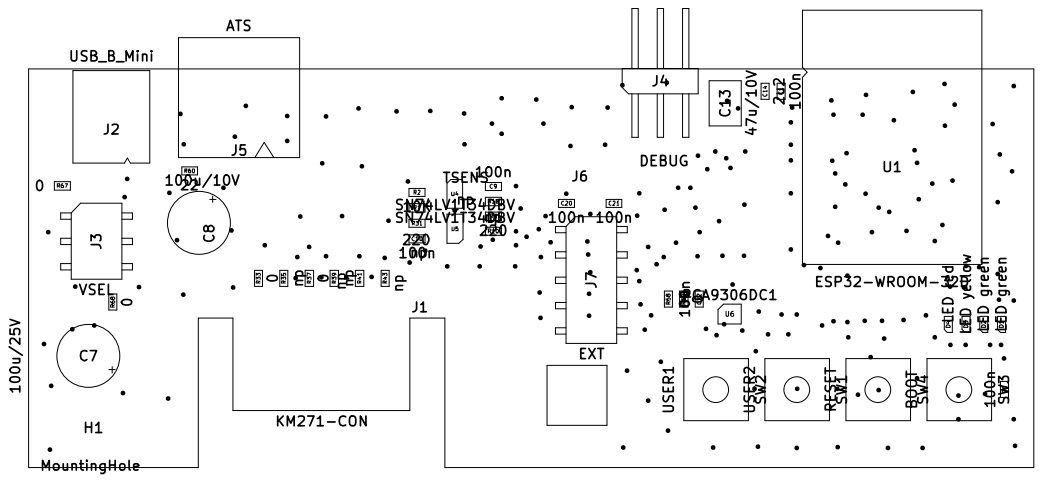
[picture p110: page 15]

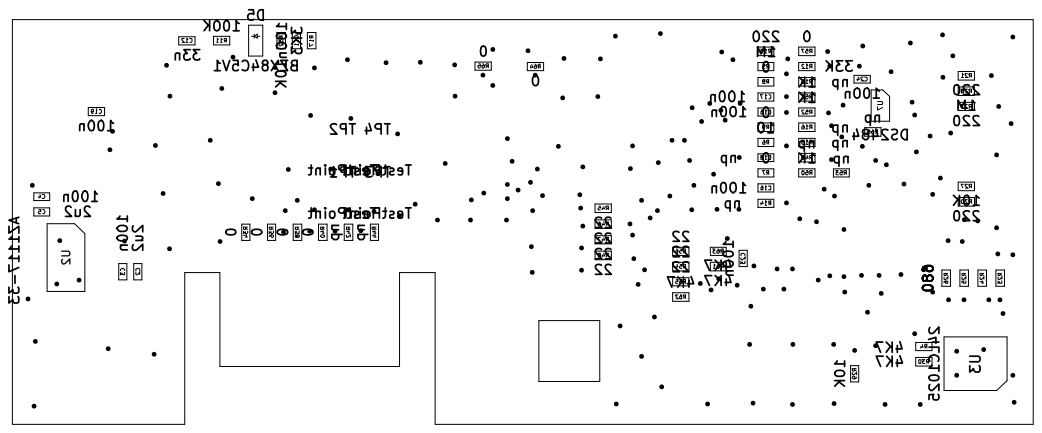
[picture p111: page 16]
